yupipi93/arduino-lemon-piano/versions/v5.5-power-filter/firmware/probe/README.md

# Board probe — v0.7.1 PCB

Not a game and not a version: a diagnostic firmware for the **assembled
v0.7.1 board**, for when it boots, lights its LEDs, and plays nothing.

```bash
# The one to use when nobody is standing at the board yet:
nohup ./run-when-ready.sh pcb 60 >/tmp/probe.log 2>&1 &

# The one to use when you ARE at the board, hand on the fruit:
./run.sh pcb              # ...or ./run.sh proto for the breadboard
```

**`run-when-ready.sh` is the default, and the reason is not politeness.** A
measurement that needs a person's hands is not ready when the machine is ready;
it is ready when the person says so. It flashes the board, sends two buttons to
Sergio's phone, and then sits there — for hours if need be — until he taps
"estoy delante". Only then does it record. `run.sh` starts recording the instant
it is launched, which is correct **only** if someone is already playing.

On 2026-09-13 an agent got this backwards: it started a 160 s capture and then
messaged him to go and play. His answer is the rule now — *"no puedes esperar
que esté yo siempre disponible, no soy una máquina, soy un humano que tiene un
hijo y responsabilidades."* The machine waits for the human, never the reverse.

> **2026-09-12, from the bench:** questions 1 and 2 below are **already
> answered** on the real board — every boot sound plays, and both SENS buttons
> beep when pressed. SENS− lives on A7 and only works through R18, a pull-up to
> `/+5V` in the same row as R1–R7, so that one press also proves **the 5 V rail
> reaches the key pull-ups**. Buzzer, buttons, LEDs and rail are all alive.
> Exactly one block is dead: the seven key channels. Question 3 is the whole
> job now, and it is the one this probe was written for.

It answers three questions in one flash, in this order:

1. **Does D13 drive BUZ1?** It beeps for 400 ms at startup, before anything can
   go wrong. D13 is also the Nano's on-board `L` LED — so *L lit, no sound* is a
   transducer fault (wrong buzzer type, or something low-impedance on J5), and
   *neither* is D13 itself or a badly seated Nano.
2. **Does the +5 V rail reach the pull-ups?** The calibration block prints each
   channel's baseline. Near **1022** is healthy. Near 0 means R1–R7 or the rail
   are not there, and it says so.
3. **Do the keys move at all, and in which direction?** All seven channels at
   10 Hz, raw value and signed delta, plus — every 10 s — the largest excursion
   since boot **in both directions** and a one-line verdict. Three outcomes,
   three different faults:

   | Verdict | Means |
   |---|---|
   | biggest movement **DOWN** | this board's polarity. The game can work; only the margin needs tuning. |
   | biggest movement **UP** | the rig is the V4/V4.5 front end (pin floating, resistor in series, player on +5 V). The game firmware cannot see it, and neither can smart adjust. |
   | **nothing moves** (≤ 2 counts) | no touch signal exists to threshold, whatever the margin says. |

   The probe is deliberately direction-agnostic because the game is not. Both
   front ends use 220 Ω — the value is the same on the breadboard and on the
   board — so "same resistors" does not mean "same circuit", and only the sign
   of the movement tells them apart.

**Run it on the breadboard too.** Same sketch, same Nano, same 9600 baud. Two
screenshots settle in a minute what no amount of reading the docs can: if the
working rig's numbers go UP and the board's do not move, the topologies differ
and that is the entire fault.

It also prints the two SENS buttons' state, which should read `up` with nothing
pressed. Permanently `DOWN` means SW1/SW2 are shorted to GND — see §4 of
[../../../../pcb/docs/REVIEW-v0.7.1-silent-keys.md](../../../../pcb/docs/REVIEW-v0.7.1-silent-keys.md).

**Why not `-DDEBUG_TOUCH` on the game build?** Because that prints only on an
*accepted* press, so it prints nothing at all when the fault is that no press is
ever accepted.

Each channel is read twice and the first conversion discarded. At 220 Ω that
changes nothing; it matters the moment the pull-ups are raised, which is the fix
the review proposes.
