yupipi93/arduino-lemon-piano/pcb/docs/DESIGN_STATE.md

# DESIGN_STATE.md — Lemon Piano V5.5 Board

**Current version: v0.7.1 — cosmetic PATCH on v0.7.0: a large
**"Created with ♥ by Multitec." maker's mark fills the top-left free
rectangle on F.SilkS (ADR-038); the board (placements, netlist, holes,
schematic) is byte-for-byte v0.7.0. v0.7.0 itself — the Nano turned back to
mini-USB WEST
(ADR-035), so the digital column is the north row and the analog column the
south row: ten-LED bar on the NORTH edge (centred on x=150, **LED1 at the
east** under D2 — ADR-036), lemon-key header on the SOUTH edge (centred,
**KEY1 west** under A0), the USB-cable corridor (x < 130.4, y 113..127)
reinstated and part-free so the cable leaves the enclosure on the left with
the module seated, and the power-entry filter folded around it — C1 ‖ C3
still adjacent on the north row, D2 + L1 moved down into the south strip with
J1 → D1 (ADR-037). Everything east of the socket (SENS±, J3/J4, BUZ1, J5) is
unchanged from v0.6.0.** (2026-09-06)

> **Flashing note (v0.7.0):** the ADR-030 cost is gone. The mini-USB faces
> west into a part-free corridor, so a cable plugs in with the Nano seated and
> clears the SENS buttons by construction. (v0.5.0–v0.6.0 needed the module
> lifted out of its socket to take a cable.)

> **VU-meter direction (ADR-036, user should know):** with the USB to the
> left, the bar fills **right→left** — LED1 (green) is at the east end, LED10
> (red) at the west. That is what a non-crossing fan under the descending
> D2..D11 row gives; the user's mock-up pasted the v0.6.0 bar (green left)
> without re-deriving it. Reversing it is a ten-line YAML change plus a
> re-route at the cost of a 45-crossing via crossbar.

> **Maker's mark (v0.7.1, ADR-038):** "Created with ♥ by Multitec." sits on
> the top-left silk (two 3.5 mm lines from x=91, spanning the left anchor). The
> heart is a FILLED SILK POLYGON, not a character — KiCad 9's stroke font has
> no U+2665 glyph (it renders as a tofu box), so it is drawn from the classic
> heart parametric. It reached the fab silkscreen gerber as a G36 region fill.

> v0.1.0 ERRATUM (ADR-015): the Nano socket rows were 180°-rotated
> (TX1/VIN assumed at the USB end; the real board has D12/D13 there).
> v0.2.0 corrected the maps. Do not fabricate v0.1.0.

## Block status

| Block | State |
|---|---|
| Nano socket (U1/U2, 2×15) | ✅ CENTRED (pin field x 132.22–167.78), **USB-west**: U1 = analog SOUTH row (pin1 D13 west, rot 90), U2 = digital NORTH row (pin1 TX1 east, rot 270). D12/D13 flank the USB at x=132.22. All 23 used pins netted, 7 NC by design |
| USB-cable corridor | ✅ x < 130.4, y 113..127 part-free on F.Cu (ADR-035 reinstates the ADR-024 band; supersedes ADR-030) — `geometry_gate` checks it against real courtyard boxes |
| Power-entry filter (J1→D1→D2→C1‖C2→L1→C3‖C4) | ✅ WEST block folded around the corridor (ADR-037): **C1 ‖ C3 adjacent** at y=106; **D2 at (107.0, 129.2)** row A; **J1 → D1 at y=136.0** row B; **L1 at (120.0, 134.5)** in its own east column; ceramics on B.Cu at y=112.5 |
| 5 V entry (J1) | ✅ 2-pin 2.54 mm header, SW corner, `+ −` silk above and `5V IN` below (ADR-025) |
| Keyboard (R1–R7 pull-ups + J2 header) | ✅ header CENTRED on the **SOUTH** edge (pin centre exactly x=150), pin 1 = KEY1 at the **WEST** under A0; silk `KEYS 1 2 3 4 5 6 7 G`; pull-ups on B.Cu at y=124.4 just north of the analog row |
| LED bar (D3–D12 + R8–R17) | ✅ **NORTH** strip, CENTRED on x=150, **LED1 EAST → LED10 WEST** (D3 at 170.7 … D12 at 129.3, matching D2..D11 which descend west→east), rot 270 so anodes point south at the row; series R on B.Cu at y=102.97 |
| UI (BUZ1 D13, SW1 SENS+ D12, SW2 SENS− A7 + R18) | ✅ unchanged east block, pair centred on y=120; buzzer NE corner. D13/D12 are at the west end again, so `/BUZZER` ≈ 60 mm and `/SENS_PLUS` ≈ 43 mm (both accepted before: ADR-027/029) |
| Aux speaker out (J5 ∥ BUZ1) | ✅ unchanged (ADR-034). **Piezo or amplified module only** |
| External-button headers (J3 ∥ SW1, J4 ∥ SW2) | ✅ unchanged (ADR-026) |
| Maker's mark (v0.7.1) | ✅ **"Created with ♥ by Multitec."** F.SilkS, top-left free rectangle (x 91..129, y 114..124), 3.5 mm / 0.40 mm stroke, heart = filled `gr_poly` (ADR-038). Left anchor divider split around it. No pad/net/copper change |
| GND | ✅ B.Cu zone, solid connect on all GND pads; refilled after the width pass (no split-net repair was needed this run) |
| Mounting (H1–H4, M2) | ✅ (95,105) / (205,105) / (95,135) / (205,135), symmetric about x=150 and y=120 |
| Schematic | ✅ mirrors PCB (48 symbols incl. 3 PWR_FLAGs), ERC 0/0. Unchanged by the flip — the pin→net map is electrical, only placements moved |
| Fab package | ✅ `pcb/releases/v0.7.1/lemon-piano-v0.7.1-fab.zip` (14 files), generated by `/fab` from the exact board every gate passed on |

## Verification snapshot (v0.7.1)

| Gate | Result |
|---|---|
| Cloud `/drc` | **0 errors, 0 warnings, 0 unconnected** (`validation/drc-v0.7.1.json`; `included_severities` = error + warning, `schematic_parity` empty) |
| ERC | 0 errors, 0 warnings (`validation/erc-v0.7.1.txt`) |
| `verify_placement` (C1 chirality, C2 flip, C3 pad↔net↔function, C4 net intent) | **74 OK / 0 FAIL** — after re-deriving both flipped 0805 groups' pad numbers from the built board (first run failed exactly there, as AGENT_PROMPT predicts) |
| `verify_holes` (geometric + VISION) | PASS — vision ran on both sides, max leave-one-out error 0.022 mm |
| `geometry_gate` (30 checks: outline, hole symmetry, USB-west orientation, LEDs north + centred + LED1 east, keys south + centred + KEY1 west, **corridor part-free**, filter-in-west, C1/C3 adjacency, button-pair centring, EXT headers east, J5-adjacent-to-BUZ1, copper per net, courtyards) | ALL PASS |
| Extra logical pass (independent script over the routed `.kicad_pcb`) | PASS — every Nano pin's net matches NETLIST.md, D12/D13 at x=132.22 (USB end), LED fan and keys fan both monotonic (no crossings), zero F.Cu pads in the corridor, all 34 nets have copper, both pin-legend rows read in true pin order |
| Render inspection (top+bottom, 4 styles) | PASS — overlay photo lands **USB-west** unrotated (PIL_rot 0), every part shows a 3D body (D1 included), LED colours 10→1 = red red orange orange yellow yellow yellow green green green west→east |
| post_route widths | 116 segments at target, 15 short pad-entry stubs capped (all ≥ 0.2 mm, worst case ≈ 200 mA); 1 dangling `/BUZZER` spur removed; no split net; 1 zone refill. 131 segments, 1 via |
| Maker's-mark silk (v0.7.1) | verified on the ROUTED board: both credit lines on F.SilkS (unmirrored, 3.5 mm), heart a 96-pt filled `gr_poly` with its point at the bottom, zero silk over any pad; the F_Silkscreen fab gerber carries the heart as a G36 region fill; render-diff vs v0.7.0 shows the two new text lines in the top-left and nothing else moved |
| Idempotency | `build_board` byte-identical across two scratch runs (`53d8c86a46ea`); routed board `65058595dd8c` |

## Iteration history

| Version | What changed | DRC (err/warn/unconn) | Verdict |
|---|---|---|---|
| v0.0.1 | first placement (no routing) | 0 / 44 / 81 | placement fits; silk collisions; renders verified |
| v0.0.2 | first freerouting pass + naive width post-pass | 12 / 44 / 9 | starved thermals on SMD GND pads; widening broke clearances |
| v0.0.3 | solid zone-connect on all GND pads; clearance-aware widener | 0 / 44 / 0 | electrically clean; silk collisions remain |
| v0.0.4 | silk labels/refs repositioned, SW refs hidden | 0 / 25 / 0 | all remaining warnings = text height < 0.8 |
| v0.0.5 | all silk text ≥ 0.8 mm | 0 / 4 / 0 | title/BUZ1 silk clashes + 1 dangling freerouting spur |
| v0.0.6 | title split, BUZ1 ref inside circle, dangling-spur cleaner | **0 / 0 / 0** | fully clean; all gates pass |
| v0.1.0 | release: schematic+ERC, gates wired into pipeline, island-healing guard, /fab | **0 / 0 / 0** | released, later found ERRATUM ADR-015 — do not fabricate |
| v0.2.0 | REAL Nano orientation (ADR-015): keys header south, LED bar north (E→W); post_route self-healing upgrades (ADR-018) | **0 / 0 / 0** | released + render suite via API v0.3.0 |
| v0.2.1 | 'pcb' version label, per-pin silk legends (both rows), all component refs visible per layer, suite naming normal/dim/realistic/overlay | **0 / 0 / 0** | released |
| v0.3.0 | 4 anchor holes (ADR-020), VU-meter LED colors + 3D bodies (ADR-021), /place model-strip bugfix (ADR-022), brighter Nano photo (ADR-023), hole VISION pass (LL §22) | **0 / 0 / 0** | released |
| v0.4.0 | 120 × 40 mm frame + floor-plan remake (ADR-024): Nano centred, keys centred south, filter folded around a USB corridor, D2 at rot=180; 2-pin 5 V header (ADR-025); parallel EXT headers J3/J4 (ADR-026); buzzer NE (ADR-027); title in the corridor (ADR-028) | **0 / 0 / 0** | released (superseded by v0.5.0) |
| v0.5.0 (run 1) | Nano FLIPPED to USB-east (ADR-029), keys north, LED bar south + centred, USB keepout dropped (ADR-030), filter refactored with C1 ‖ C3 adjacent (ADR-031) | 2 / 0 / 0 | **FAILED the DRC gate** — two `/+5V` bus bridges laid on filled ground |
| v0.5.0 (run 2) | post_route now refills the GND zone after split-net repair (ADR-032) | **0 / 0 / 0** | released |
| v0.5.1 | D1's 3D body restored (ADR-033). Cosmetic only | **0 / 0 / 0** | released |
| v0.6.0 | J5: 2-pin aux speaker output in parallel with the buzzer (ADR-034) | **0 / 0 / 0** | released |
| v0.7.0 (run 1) | Nano turned back to **USB-west** for enclosure cable access (ADR-035, supersedes ADR-029/030): LEDs north with LED1 east, keys south with KEY1 west (ADR-036), USB corridor reinstated, D2 + L1 moved to the south strip (ADR-037) | **0 / 0 / 0** | DRC/ERC/renders/3D green; **stopped at `verify_placement`** — both 0805 groups' pad numbers inverted with the flip (expected, AGENT_PROMPT step 2) |
| v0.7.0 (gates re-run) | `ground-truth/components.yaml` pad numbers re-derived from the built board (no board change); verify_placement 74/0, verify_holes + vision PASS, geometry_gate 30/30; `/fab` on that same board | **0 / 0 / 0** | released |
| v0.7.1 | cosmetic silk PATCH: "Created with ♥ by Multitec." maker's mark, top-left, heart as a filled polygon (ADR-038). No placement/net/hole change — all three gates identical to v0.7.0 | **0 / 0 / 0** | **RELEASED** |

(One v0.1.0 route attempt produced a GND-zone island — caught by the
DRC gate, fixed by the automatic island healing, re-run clean. Kept in
`validation/` history.)

## How to regenerate

```bash
# full iteration (build → /place → /route → post → /drc → /render → gates):
./pcb/tools/cloud_pipeline.sh v0.7.1
# release (adds /fab):
./pcb/tools/cloud_pipeline.sh v0.7.1 --fab
```

Note on v0.7.0's release: the fab package was produced by calling `/fab`
directly on the board that had just passed every gate, rather than by a
`--fab` re-run of the whole pipeline. Freerouting is stochastic, so a
re-run would have routed a *different* board and needed the full gate set
again; fabbing the verified artefact keeps the release byte-consistent with
the committed `.kicad_pcb` (the v0.5.0 lesson in AGENT_PROMPT).

## Open items

- Bench-validate the filter on the physical board (the V5.5 repo's own
  pending check — switch-flipping session with the V5 bench sampler).
- **VU-meter direction** (ADR-036): the bar fills right→left with the USB on
  the left. If the user prefers green-left, reverse D3..D12 / R8..R17 /
  the B.SilkS LED refs in the YAML and re-route (expect ~10 vias and a
  carved B.Cu plane under the north row).
- The mini-USB plug's overmold is ~11 mm wide; the corridor reserves ±7 mm
  about y=120 on F.Cu. Tracks do cross it (that is by design), so a
  right-angle plug is fine but nothing tall may ever be placed there again.
- The 15 capped stubs (ADR-008) are ≥ 0.2 mm and current-safe.
- **J5 drives what D13 drives**, i.e. a high-impedance piezo (ADR-034).
- `/VRAW` and `/+5V` now run ≈ 30 mm north–south side by side through the
  west block (ADR-037). Acceptable for a conducted-transient filter; the
  C1—L1—C3 series order of ADR-031's note remains the fix if HF isolation
  is ever needed.
- Largest free areas: the region under the Nano body on both layers and the
  east half of the south strip (x 128–139, y 129–140) beside L1.
