yupipi93/arduino-lemon-piano/pcb/docs/NETLIST.md

# NETLIST.md — Lemon Piano V5.5 Board

Ground truth for the PCB. Extracted 2026-07-30 from the `arduino-lemon-piano`
repo — **no value, pin or part invented here**. Sources:

| Source | What it fixes |
|---|---|
| `versions/v5.5-power-filter/HARDWARE.md` | power-entry filter chain, part values, BOM delta |
| `versions/v5-led-bar/HARDWARE.md` (pin map, 2026-07-28) | every Nano pin assignment |
| `tools/wiring_diagrams.py` → `build_v5_5()` (DRC-validated wirewright contract) | the authoritative net list (58 nets rendering, 0 violations) |

> The V5 HARDWARE.md *BOM table* contains two stale rows ("Passive buzzer D8",
> "SENS + on D7"). The 2026-07-28 pin map in the same file and the
> `build_v5_5()` contract agree and override them: **buzzer = D13,
> SENS + = D12, SENS − = A7**. Recorded in DECISIONS.md (ADR-001).

## Circuit summary

V5 game board (7 lemon keys pulled up 220 Ω to the rail, player holds GND;
ten-LED progress bar on D2–D11; SENS± buttons; passive buzzer) **plus** the
V5.5 power-entry filter: 5 V in → P6KE6.8A TVS shunt → 1N5817 series Schottky
→ 470 µF ‖ 100 nF → 100 µH power choke → 470 µF ‖ 100 nF → the +5 V rail
(also AVcc = ADC reference — that is the whole point of the filter).

The Nano is **socketed**: two 1×15 2.54 mm female rows (U1/U2). Since v0.7.0
the mini-USB end faces the **WEST** board edge again (ADR-035, undoing the
v0.5.0 flip): the cable leaves the enclosure on the left, clear of the button
block, and a part-free corridor (x < 130.4, y 113..127) lets it be plugged in
with the module seated. USB power still stays behind the 1N5817 so it cannot
back-feed the filter (`HARDWARE.md` powering rule 2).

**v0.4.0 circuit deltas** (user spec 2026-07-30, ADR-024…027) — the V5.5
circuit itself is unchanged; only the board interface grew:

- 5 V entry is a **2-pin 2.54 mm header** (J1) instead of the Phoenix screw
  terminal. Same two nodes, same polarity (pad 1 = +, pad 2 = GND).
- Two **external-button headers** (J3, J4) are wired in **parallel** with
  SW1/SW2. Shorting a header's two pins is electrically identical to
  pressing the on-board button, so a panel-mounted button can be added
  without cutting a trace.
- **v0.6.0**: an **auxiliary speaker header** (J5) is wired in **parallel**
  with the buzzer — pad 1 on /BUZZER, pad 2 on /GND. It carries the raw D13
  drive, so it suits another passive piezo or an *amplified* speaker module;
  a bare 4–8 Ω voice coil must not be connected directly (ADR-034).

## Components (29 + 18 R + 4 H = 51 footprints)

| Ref | Value | Footprint (KiCad 9 lib) | Source line |
|---|---|---|---|
| U1 | Nano socket row A — the **analog** column (Nano pins 16–30: D13,3V3,AREF,A0…A7,5V,RST,GND,VIN) | `Connector_PinSocket_2.54mm:PinSocket_1x15_P2.54mm_Vertical` | v5 HARDWARE pin map |
| U2 | Nano socket row B — the **digital** column (Nano pins 1–15: TX1,RX0,RST,GND,D2…D12) | idem | idem |
| J1 | 5V_IN 1×2 header | `Connector_PinHeader_2.54mm:PinHeader_1x02_P2.54mm_Vertical` | v5.5 BOM "5 V input pigtail" → 2-pin header (ADR-025, supersedes ADR-003) |
| J2 | LEMON_KEYS 1×8 header (KEY1…KEY7 + GND) | `Connector_PinHeader_2.54mm:PinHeader_1x08_P2.54mm_Vertical` | keys A0–A6 + GND clip (ADR-004) |
| J3 | SENS+_EXT 1×2 header (parallel to SW1) | `Connector_PinHeader_2.54mm:PinHeader_1x02_P2.54mm_Vertical` | user spec 2026-07-30 (ADR-026) |
| J4 | SENS−_EXT 1×2 header (parallel to SW2) | idem | idem |
| J5 | SPK_OUT 1×2 header (parallel to BUZ1) | idem | user spec 2026-07-31 (ADR-034) |
| D1 | P6KE6.8A (TVS, 600 W) | `Diode_THT:D_DO-15_P5.08mm_Vertical_KathodeUp` | v5.5 HARDWARE filter table |
| D2 | 1N5817 (Schottky) | `Diode_THT:D_DO-41_SOD81_P5.08mm_Vertical_AnodeUp` | idem |
| C1 | 470u/16V (input reservoir) | `Capacitor_THT:CP_Radial_D8.0mm_P3.50mm` | idem |
| C2 | 100nF X7R (input ceramic) | `Capacitor_SMD:C_0805_2012Metric_Pad1.18x1.45mm_HandSolder` | idem + CONVENTIONS §4 |
| L1 | 100uH ≥1 A power choke (e.g. Fastron 07HCP-101K, 1.3 A) | `Inductor_THT:L_Radial_D8.7mm_P5.00mm_Fastron_07HCP` | idem ("drum or toroid, ≥1 A") |
| C3 | 470u/16V (output reservoir) | `Capacitor_THT:CP_Radial_D8.0mm_P3.50mm` | idem |
| C4 | 100nF X7R (output ceramic) | 0805 HandSolder | idem |
| R1–R7 | 220 (key pull-ups KEY1…KEY7 = A0…A6) | `Resistor_SMD:R_0805_2012Metric_Pad1.20x1.40mm_HandSolder` | v5 HARDWARE "220 Ω pull-up per key" |
| R8–R17 | 220 (LED series, LED1…LED10) | idem | v5 HARDWARE "one per LED" |
| R18 | 10k (SENS− external pull-up on A7) | idem | v5 HARDWARE "A7 has no internal pull-up" |
| D3–D12 | LED 1…10: 3×GREEN, 3×YELLOW, 2×ORANGE, 2×RED | `LED_THT:LED_D3.0mm` (colored 3D bodies per LED, ADR-021) | v5 HARDWARE "Green LEDs ×10"; VU-meter colors per user spec 2026-07-30 |
| BUZ1 | passive buzzer | `Buzzer_Beeper:Buzzer_12x9.5RM7.6` | v5 HARDWARE (D13) + CONVENTIONS §5 |
| SW1 | SENS + push button (D12, to GND, internal pull-up) | `Button_Switch_THT:SW_PUSH_6mm` | v5 HARDWARE pin map |
| SW2 | SENS − push button (A7, to GND, R18 pull-up) | idem | idem |
| H1–H4 | M2 mounting hole | `MountingHole:MountingHole_2.5mm_Pad_Via` | board spec v0.3.0 (2 per short edge, ADR-020) |

## Board frame (v0.7.0)

120 × 40 mm, KiCad frame x 90..210 / y 100..140, centre (150, 120). The
Nano pin field is centred on the board (x 132.22..167.78, rows y 112.38 /
127.62) with the **mini-USB facing WEST** (ADR-035); that puts the digital
column on the north row and the analog column on the south row.
Consequently the LED bar sits on the NORTH edge (centred on x = 150, LED1 at
the east under D2) and the keys header on the SOUTH edge (centred, pin centre
exactly x = 150, KEY1 at the west under A0). The power-entry filter occupies
the west block folded around the USB-cable corridor (x < 130.4, y 113..127,
part-free on F.Cu): C1 ‖ C3 on the north row, D2 / J1 → D1 / L1 in the south
strip (ADR-037).

## Nano socket pin map (physical, USB end = WEST) — v0.7.0, ADR-035

The Nano's own pinout is fixed (ADR-015: D12/D13 flank the mini-USB,
TX1/VIN sit at the ICSP end). v0.7.0 turns the module 180° in-plane back to
USB-west (v0.5.0/v0.6.0 were USB-east), which swaps BOTH which row carries
which column AND the west→east pin order:

```
U2 (NORTH row, y=112.38), pin1 → pin15 runs EAST → WEST:
   TX1 RX0 RST GND D2 D3 D4 D5 D6 D7 D8 D9 D10 D11 D12
   x:  167.78 …………………………………………………………………… 132.22
        [ mini-USB faces x=90 west edge ]
U1 (SOUTH row, y=127.62), pin1 → pin15 runs WEST → EAST:
   D13 3V3 AREF A0 A1 A2 A3 A4 A5 A6 A7 5V RST GND VIN
   x:  132.22 …………………………………………………………………… 167.78
```

Digitals land on the NORTH row **descending** west→east (D2 at 157.62 …
D11 at 134.76) → LED bar on the NORTH edge with **LED1 at the EAST** under
D2 and LED10 at the west under D11, so the fan does not cross (ADR-036).
Analogs land on the SOUTH row **ascending** west→east (A0 at 139.84 … A6 at
155.08) → keys header on the SOUTH edge with **J2 pin 1 (KEY1) at the WEST**
under A0 (x 141.11 vs 139.84). D13 and D12 sit at the WEST end flanking the
USB, so `/BUZZER` (D13 → BUZ1 in the NE corner) is long again, as in v0.4.0
and accepted in ADR-027, and so is `/SENS_PLUS` (D12 → SW1).

## Historical pin map (USB end = EAST) — v0.5.0 … v0.6.0, ADR-029

Flipping the module 180° in-plane swapped BOTH which row carried which
column AND the west→east pin order:

```
U1 (NORTH row, y=107.38+5 → 112.38), pin1 → pin15 runs EAST → WEST:
   D13 3V3 AREF A0 A1 A2 A3 A4 A5 A6 A7 5V RST GND VIN
   x:  167.78 …………………………………………………………………… 132.22
        [ mini-USB faces x=210 east edge ]
U2 (SOUTH row, y=127.62), pin1 → pin15 runs WEST → EAST:
   TX1 RX0 RST GND D2 D3 D4 D5 D6 D7 D8 D9 D10 D11 D12
   x:  132.22 …………………………………………………………………… 167.78
```

Analogs land on the NORTH row → keys header on the NORTH edge, with
J2 pin 1 (KEY1) at the EAST under A0 (x 158.89 vs 160.16) so the fan does
not cross. Digitals land on the SOUTH row ascending west→east → LED bar on
the SOUTH edge ascending west→east (LED1 west under D2, LED10 east under
D11). D13 and D12 now sit at the EAST end, next to the buzzer and the
SENS+ button respectively — much shorter runs than v0.4.0.

## Historical pin map (USB end = WEST) — v0.2.0 … v0.4.0, ADR-015

**Erratum fixed in v0.2.0**: v0.1.0 assumed TX1/VIN at the USB end (a
misread pinout diagram). The REAL Nano — verified on the official 2008
Arduino Nano V2.2 photo (Wikimedia `File:ArduinoNanoTop.jpg`) and on
clone boards (`File:Arduino Nano.jpg`) — has **D12/D13 flanking the
mini-USB and TX1/VIN at the ICSP end**. With the USB facing WEST:

```
   x=104                                                    x=139.56
U2: D12 D11 D10 D9 D8 D7 D6 D5 D4 D3 D2 GND RST RX0 TX1   (y=107.38, pin15→pin1)
        [ mini-USB faces x=90 west edge ]
U1: D13 3V3 AREF A0 A1 A2 A3 A4 A5 A6 A7 5V RST GND VIN   (y=122.62, pin1→pin15)
```

`U1` = SOUTH row, pin 1 (D13) west; `U2` = NORTH row, pin 1 (TX1) east.
Analogs land on the SOUTH row → keys header on the SOUTH edge; digitals
on the NORTH row → LED bar on the NORTH edge (both flipped vs v0.1.0).

## Nets (KiCad net number → name → pads)

| # | Net | Pads |
|---|---|---|
| 1 | /+5V | U1.12 (5V), L1.2, C3.1(+), C4.1, R1.2…R7.2, R18.2 |
| 2 | /GND | U1.14, U2.4, J1.2, J2.8, J3.2, J4.2, J5.2, D1.2(A), C1.2(−), C2.2, C3.2(−), C4.2, R8.1…R17.1, BUZ1.2, SW1.2(×2), SW2.2(×2), H1.1…H4.1 |
| 3 | /VIN | J1.1(+), D1.1(K), D2.2(A) |
| 4 | /VRAW | D2.1(K), C1.1(+), C2.1, L1.1 |
| 5–11 | /KEY1…/KEY7 | U1.4…U1.10 (A0…A6), R1.1…R7.1, J2.1…J2.7 (KEY1=J2.1 … KEY7=J2.7) |
| 12 | /SENS_MINUS | U1.11 (A7), R18.1, SW2.1(×2), J4.1 |
| 13 | /SENS_PLUS | U2.15 (D12), SW1.1(×2), J3.1 |
| 14 | /BUZZER | U1.1 (D13), BUZ1.1(+), J5.1 |
| 15–24 | /LED1…/LED10 | U2.5…U2.14 (D2…D11) → D3.2…D12.2 (anodes) |
| 25–34 | /LED1_K…/LED10_K | D3.1…D12.1 (cathodes) → R8.2…R17.2 |

Unconnected (by design): U2.1 (TX1), U2.2 (RX0), U2.3 (RST), U1.2 (3V3),
U1.3 (AREF), U1.13 (RST), U1.15 (Nano VIN — the filtered rail feeds the 5V
pin directly, exactly like the breadboard rail; VIN would insert the Nano's
own regulator and drop the 4.7 V rail further).

Wirewright-contract cross-check (`build_v5_5`): net `vin` = {J1.vout,
DTVS.cathode, DS.anode} ✓ /VIN; `vraw` = {DS.cathode, CF1.a, CF2.a, LF1.a} ✓
/VRAW; `vfilt` = {LF1.b, CF3.a, CF4.a, rail 5V} ✓ /+5V; `pgnd` + `nanognd` +
key/button/LED grounds ✓ /GND; `kn0..kn6` (pin+fruit clip+pull-up low side)
✓ /KEY1…7; `a0..a9`/`c0..c9`/`g0..g9` ✓ /LEDn + /LEDn_K; `buzsig` ✓ /BUZZER;
`SUPsig` ✓ /SENS_PLUS; `sdnsig` (A7+button+R.b) ✓ /SENS_MINUS; `sdnpu`/`kp*`
(pull-up highs) ✓ /+5V. All 58 diagram nets accounted for.

## Current / width budget

Worst case board draw ≈ 200 mA (10 LEDs ≈ 150 mA + Nano ≈ 30 mA + margin —
v5 HARDWARE "All ten lit ≈ 150 mA"). Power path (VIN→VRAW→+5V, GND returns)
routed at 0.5 mm (≥ 0.4 spec); signals 0.25 mm. LED/key currents ≤ 15 mA.
