yupipi93/arduino-lemon-piano/docs/GUIA-DE-USO.es.md

# 🍋 Piano de limones — cómo se toca

*La hoja de instrucciones, pensada para imprimirse y dejarse al lado del piano.
Explica la caja que tienes delante y no da por supuesto nada del código de
dentro.*

> Este repositorio se escribe en inglés; el original de esta hoja es
> [USER-GUIDE.md](USER-GUIDE.md) y es la fuente. Esta traducción existe porque
> lo que se imprime lo lee gente, y la gente que lo va a leer habla español.
> Si las dos discrepan, manda la inglesa.

Vale para la placa **V5.5** (la que va en la carcasa impresa) con el firmware
del 09-09-2026.

---

## 1. Montarlo

1. Clava un clavo en cada uno de los siete limones y engancha un cable a cada
   clavo, de izquierda a derecha: son las teclas **1** a **7**.
2. El octavo cable — el que sobra — va a la **pinza**, y **la pinza se sujeta
   con la mano**. No es opcional: tú eres la mitad del circuito. Hasta que
   alguien no la tiene en la mano, no funciona nada.
3. Aliméntalo con un **cargador de pared USB**, no con un portátil. El ruido de
   masa de un ordenador se salta el filtro y el piano empieza a tocar solo.
4. Toca un limón con la otra mano. Suena.

> **Si no pasa nada, o si toca sin que lo toquen**, vete al §6 *Ajuste*. La
> fruta cambia según se seca; el piano está hecho para reajustarse.

## 2. Al encenderlo

La barra de diez luces se llena sola durante un par de segundos y suena una
moneda por cada limón. Eso es la **calibración**: está midiendo qué aspecto
tiene "no me están tocando" en cada limón.

**No toques la fruta mientras corren las luces.** Si tienes un limón cogido
durante esos dos segundos, aprende eso como lo normal y esa tecla se queda
sorda.

Una fanfarria corta y después una melodía: así te dice **en qué modo ha
arrancado**. Siempre arranca en el **nivel 1**.

## 3. El juego

Cada nivel esconde una **melodía secreta de diez notas**. Hay que encontrarla de
oído.

- Toca limones libremente: no pasa nada malo y la barra sigue vacía.
- En cuanto aciertes la **primera nota de la melodía secreta**, se enciende la
  luz 1. Ya estás dentro.
- Cada nota correcta enciende la siguiente. **1 → 10.**
- Una nota equivocada **apaga la barra entera** y hay que empezar la melodía de
  nuevo. Primero oyes la nota que has tocado y después el sonido de error, así
  que siempre sabes qué limón ha sido.
- Enciende las diez y suena el tema del nivel, con las luces subiendo, después
  la fanfarria del mástil — y **el siguiente nivel empieza solo**.
- Al superar el nivel 4 la melodía final se repite en bucle hasta que la pares
  (ver §5).

**Tocar el mismo limón dos veces seguidas no es un fallo: simplemente no
cuenta.** La nota suena igual de bien; el juego no la está escuchando, porque ya
está esperando un limón *distinto*.

Y se ve que no ha contado: **se encienden todas las luces a la vez** mientras
tienes ese limón tocado, y en cuanto lo sueltas tu marcador vuelve exactamente
como estaba. Diez luces encendidas nunca son un marcador: diez es ganar, y al
ganar no te quedas con el dedo puesto. No pierdes nada, no se te resta nada, y
ya no hay sonido de regañina: ese traqueteo se ha quitado (13-09-2026).
Compáralo con una nota equivocada, que **apaga la barra y la deja apagada**: no
se pueden confundir.

## 4. Modo libre — el piano sin juego

El modo libre no es un nivel y **no se llega a él jugando**. **Mantén pulsado el
botón + tres segundos** y el piano cambia el juego por el instrumento. Vuelve a
mantenerlo y el juego regresa, al nivel que dejaste.

En modo libre los siete limones son sencillamente las notas de toda la vida:

| Limón | 1 | 2 | 3 | 4 | 5 | 6 | 7 |
|---|---|---|---|---|---|---|---|
| Nota | **do** | **re** | **mi** | **fa** | **sol** | **la** | **si** |
| | C5 | D5 | E5 | F5 | G5 | A5 | B5 |

- Ni melodía secreta, ni notas equivocadas, ni nada que ganar.
- **Puedes repetir el mismo limón las veces que quieras**: aquí la regla de "una
  sola vez" está desactivada, porque es justo lo contrario de lo que necesita un
  instrumento.
- **Si mantienes el limón, la nota se mantiene: una nota, no un tartamudeo.**
  Suelta de verdad y vuelve a tocar para que suene otra vez. Tocar rápido sigue
  funcionando; sólo ignora el parpadeo de un dedo que nunca se fue.
- **Cada nota rompe una ola.** Al tocar un limón sale una ola de luz desde el
  sitio que ese limón ocupa en la barra: el limón 1 la manda de izquierda a
  derecha, el 7 de derecha a izquierda, y uno del medio la abre hacia los dos
  lados a la vez.
- Y eso es **todo** lo que hacen las luces aquí: pasa la ola y la barra se
  vuelve a apagar. No se queda nada encendido mientras mantienes la nota.
- **Dos limones a la vez suenan como dos notas.** Mantén un segundo limón junto
  al primero y suena el intervalo, con la barra enseñando dos luces separadas,
  una por nota. Suelta cualquiera de los dos y el otro sigue sonando. Hacen
  falta dos toques de verdad: un dedo apoyado cerca del limón vecino no vale, y
  eso es a propósito.
- Cuando no estás tocando, la barra está **apagada**. Toda luz que veas la ha
  encendido tu dedo.
- Entrar en modo libre lo anuncia la propia barra: dos luces entran desde los
  extremos, se encuentran, se abren hasta encender la barra entera y se apagan
  — y después el piano te toca la escala.

### ¿Se te ha olvidado cómo iba la melodía? Pídela otra vez

**Toca el mismo limón cinco veces seguidas** y el nivel te vuelve a tocar su
melodía, la misma con la que empezó. En esa melodía está escondida la clave
secreta, así que esto es el botón de pista.

**La nota que acabas de tocar cuenta como la primera**, así que en la práctica
son cuatro toques más sobre el limón que ya tienes debajo del dedo. Toca,
suelta, vuelve a tocar; sin pararte, porque si dejas más de segundo y medio
entre dos toques la cuenta empieza de cero.

No molesta al juego: las luces vuelven exactamente como estaban y sigues por
donde ibas. Y hay una forma de que te salga gratis: **repite el limón que el
juego acaba de aceptar.** Tocar dos veces el mismo limón nunca cuenta para
nada, así que hecho de esa manera la pista no te cuesta absolutamente nada.

En modo libre no está, a propósito: tocar un limón una y otra vez es
precisamente para lo que existe el modo libre.

## 5. Elegir modo

Todo lo de aquí abajo se hace con los dos botones: **+** y **−**. La regla que
los hace fáciles de recordar: **un toque es la sensibilidad, una pulsación larga
es un modo.**

### El interruptor del instrumento — mantener **+**

**Mantén pulsado el botón + tres segundos.** Desde el primer segundo la barra se
llena y suena un pitido que sube, igual que en la rueda de abajo, así que
siempre sabes que está cargando. A los tres segundos el piano cambia:

- si estabas jugando un nivel → **modo libre**, anunciado con una escala
  do-re-mi-fa-sol-la-si
- si estabas en modo libre → **vuelta al nivel que dejaste**, anunciado con su
  propio tema

Si lo sueltas antes, no pasa nada. Es un interruptor, así que el mismo gesto te
lleva en los dos sentidos: nunca tienes que buscar un menú para recuperar tu
instrumento.

### La rueda de niveles — mantener **−**

**Mantén pulsado el botón − y no lo sueltes.** Al segundo, el piano empieza a
cargar: la barra se llena y suena un pitido que va subiendo. A los **tres
segundos** las luces hacen un barrido de ida y vuelta, suena un aviso de tres
notas ascendentes y ya estás dentro.

Si lo sueltas antes de los tres segundos no pasa nada: oirás un golpe doble
grave que significa "cancelado". *(La pulsación en sí baja la sensibilidad un
paso, como haría cualquier −; en cuanto se convierte en cambio de modo, ese paso
se devuelve.)*

### Girarla

**Un toque en +** para el nivel siguiente, **un toque en −** para el anterior. Es
una rueda: pasado el nivel 4 se vuelve al 1. El modo libre **no está en la
rueda** — es la pulsación larga de **+**, así que girar la rueda nunca te puede
quitar el instrumento.

Cada parada te dice dónde estás, por partida doble:

| Modo | Luces | Sonido |
|---|---|---|
| Nivel 1 | **1** luz, parpadeando | el tema Overworld |
| Nivel 2 | **2** luces, parpadeando | el tema Underworld |
| Nivel 3 | **3** luces, parpadeando | el tema de la estrella |
| Nivel 4 | **4** luces, parpadeando | el tema del castillo |

Las luces que parpadean son *una pregunta*; las fijas son *un marcador*. "Cuatro luces
parpadeando".

Si vuelves a pulsar mientras suena una melodía, se corta al momento y pasa a la
siguiente: nunca hay que esperar a la música.

### Elegirla

**Pulsa los dos botones a la vez.** Ni el orden ni la precisión importan: pulsa
uno y después el otro cuando quieras. Suena una confirmación corta y arranca el
modo.

Elegir un **nivel** lo empieza desde cero, con la barra vacía. Elegir **modo
libre** te entrega el instrumento.

### Salir sin elegir

Tres maneras, y ninguna cambia nada:

- **Mantén cualquiera de los dos botones tres segundos**: suena el aviso de
  entrada al revés.
- **Márchate.** A los veinte segundos sin tocar un botón se cierra sola.
- **Elige el modo en el que ya estabas**: la rueda se abre justo en el modo que
  estás jugando, así que abrir y aceptar sin más no hace absolutamente nada.

El juego se queda exactamente como lo dejaste: mismo nivel, mismas luces, mismo
progreso.

## 6. Ajuste — cuando la fruta deja de portarse bien

El piano detecta un contacto como una **caída de tres o cuatro cuentas** sobre
1024. Es una señal minúscula, y cambia con la fruta, con la habitación y con tus
manos.

| Síntoma | Qué hacer |
|---|---|
| Los limones no responden | Da unos toques a **+** (más sensible) |
| Toca notas él solo | Da unos toques a **−** (menos sensible) |
| Ni una cosa ni la otra | **Ajuste inteligente**, aquí abajo |
| No funciona absolutamente nada | ¿Tienes la pinza en la mano? ¿Está enchufado a un cargador de pared? |

Cada toque mueve un paso y la barra te enseña dónde queda el ajuste; el tono del
pitido sube según se vuelve más sensible, así que se puede ajustar sin mirar.
Deja el botón pulsado para recorrer los pasos deprisa.

**Ajuste inteligente** — el bueno. **Toca un limón y no lo sueltes**, y entonces
mantén **los dos botones un segundo**. La barra se llena mientras escucha, y
deduce el mejor ajuste con tu dedo de verdad sobre tu fruta de verdad.

- Un acorde ascendente (**1-up**) = ha aprendido algo. Ya está.
- Un traqueteo descendente = no ha podido distinguir tu contacto del ruido, y
  **no ha cambiado nada**. Comprueba que tienes la pinza en la mano y repite.

> **Las tres pulsaciones largas, y cómo no confundirlas.** *Los dos* botones un
> segundo = ajustar. *Sólo* **+** tres segundos = el interruptor del instrumento.
> *Sólo* **−** tres segundos = la rueda de niveles. No pueden chocar: si vas a
> por el segundo botón a media carga, la carga se cancela y le cede el turno al
> ajuste.

Para empezar del todo de cero, **desenchufa y vuelve a enchufar**. Eso repite la
calibración y vuelve al nivel 1.

## 7. Todos los gestos, uno por línea

| Gesto | Qué hace |
|---|---|
| Toque en **+** | Más sensible, un paso — **una luz más** |
| Toque en **−** | Menos sensible, un paso — **una luz menos** |
| Mantener **+** **3 s** | **Modo libre ⇄ el nivel** |
| Mantener **−** **3 s** | **Abre la rueda de niveles** |
| En la rueda: toque en **+** / **−** | Nivel siguiente / anterior (da la vuelta) |
| En la rueda: **los dos botones** | Elegir este nivel |
| En la rueda: mantener cualquiera **3 s** | Salir sin cambiar nada |
| Mantener **los dos** **1 s** tocando un limón | Ajuste inteligente |
| Mantener **los dos** **1 s** durante la melodía final | Volver al nivel 1 |
| Desenchufar y enchufar | Reinicio completo, recalibra |

## 8. Los sonidos y lo que significan

Todo sonido que no es una nota es un efecto de Super Mario Bros, y está
afinado **por encima** de los limones para que nunca se confunda con una nota.

| Sonido | Significado |
|---|---|
| Moneda, una por limón | Calibrando: manos fuera |
| Champiñón (power-up) | Calibración terminada, adelante |
| Pitidos que suben | Un botón está cargando: **+** el interruptor del instrumento, **−** la rueda de niveles |
| Tres notas ascendentes | La rueda está abierta |
| Las mismas tres, descendentes | La rueda se cerró sin cambiar nada |
| Quinta que resuelve en la octava | Has elegido un modo |
| Golpe doble grave | Fin del recorrido, o carga cancelada |
| Estertor corto de muerte | Nota equivocada |
| 1-up | El ajuste inteligente ha aprendido algo |
| Melodía de muerte completa | El ajuste inteligente no ha podido; no ha cambiado nada |
| Fanfarria del mástil | Nivel superado |

---

*Códigos secretos, tablas de notas y el porqué de cada tiempo de arriba:
[../versions/v5.5-power-filter/README.md](../versions/v5.5-power-filter/README.md).*
