yupipi93/arduino-lemon-piano/pcb/renders/INDEX.md

# Renders gallery — renders

> Auto-generated by `pcb-designer gallery renders`. Edit the YAML config or re-run the renderer to update — do NOT hand-edit this file.

Versions catalogued: **36**

## v0.7.1 — realistic

| top | bottom |
|---|---|
| v0.7.1 top | v0.7.1 bottom |

## v0.7.1 — overlay

| top | bottom |
|---|---|
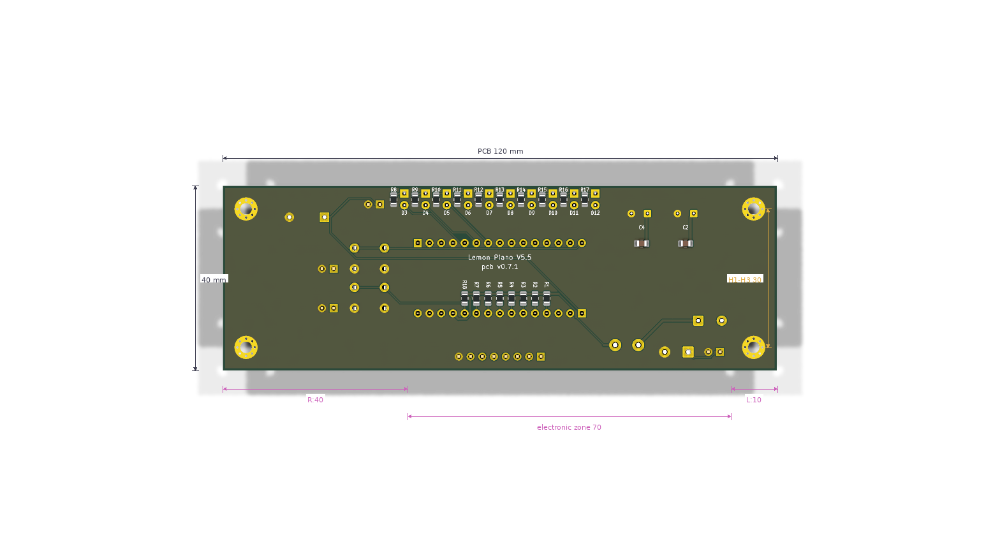
[picture p25: pcb/renders/v0.7.1-overlay-bottom.png]
v0.7.1 bottom
| v0.7.1 top |  |

## v0.7.1 — normal

| top | bottom |
|---|---|
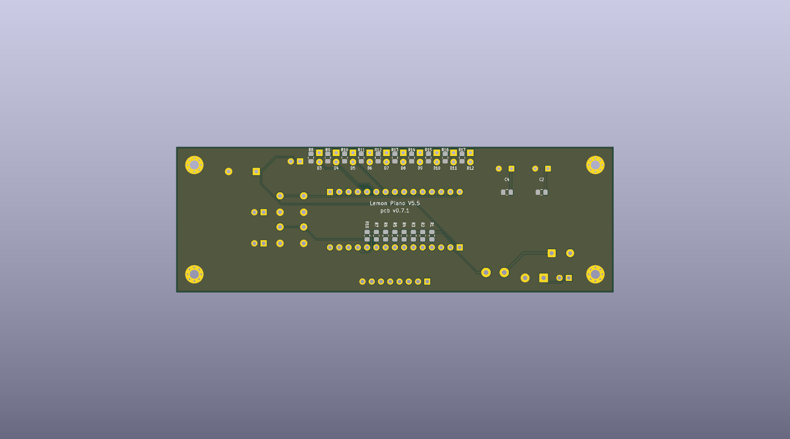
[picture p26: pcb/renders/v0.7.1-normal-bottom.png]
v0.7.1 bottom
| v0.7.1 top |  |

## v0.7.1 — dim

| top | bottom |
|---|---|
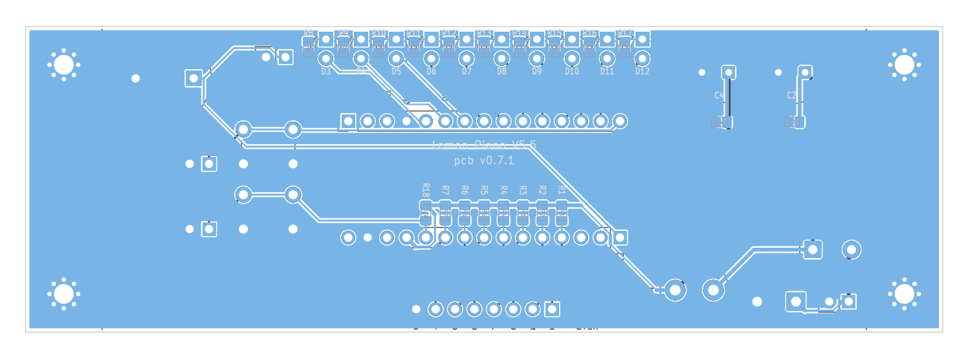
[picture p27: pcb/renders/v0.7.1-dim-bottom.png]
v0.7.1 bottom
| v0.7.1 top |  |

## v0.7.0 — realistic

| top | bottom |
|---|---|
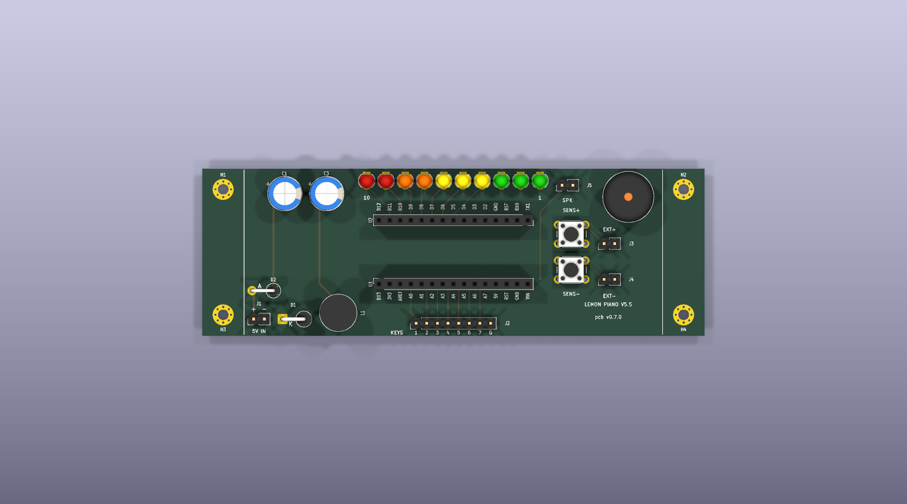
[picture p28: pcb/renders/v0.7.0-realistic-top.png]
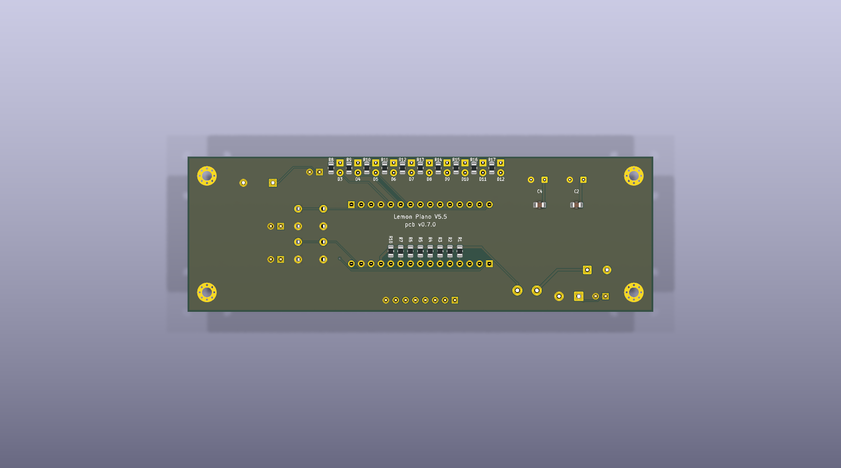
[picture p29: pcb/renders/v0.7.0-realistic-bottom.png]
v0.7.0 bottom
|  |  |

## v0.7.0 — overlay

| top | bottom |
|---|---|
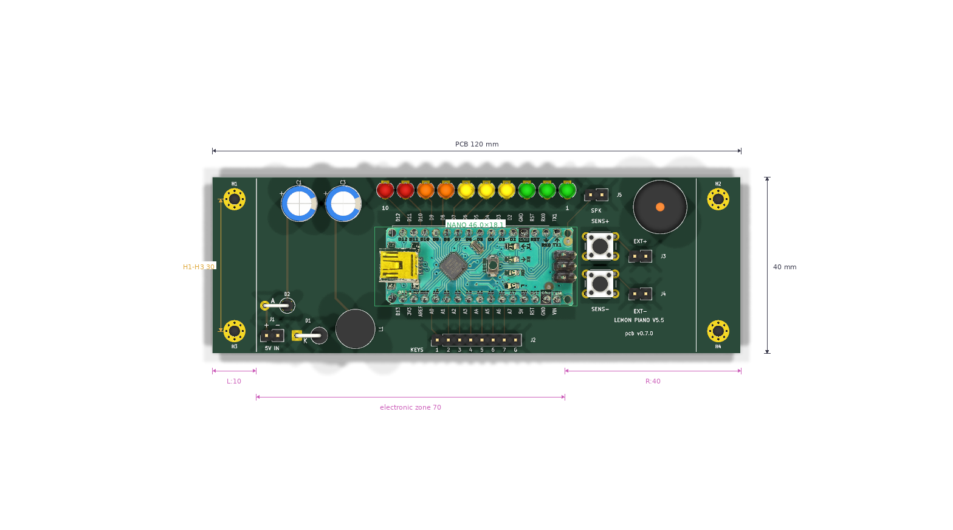
[picture p30: pcb/renders/v0.7.0-overlay-top.png]
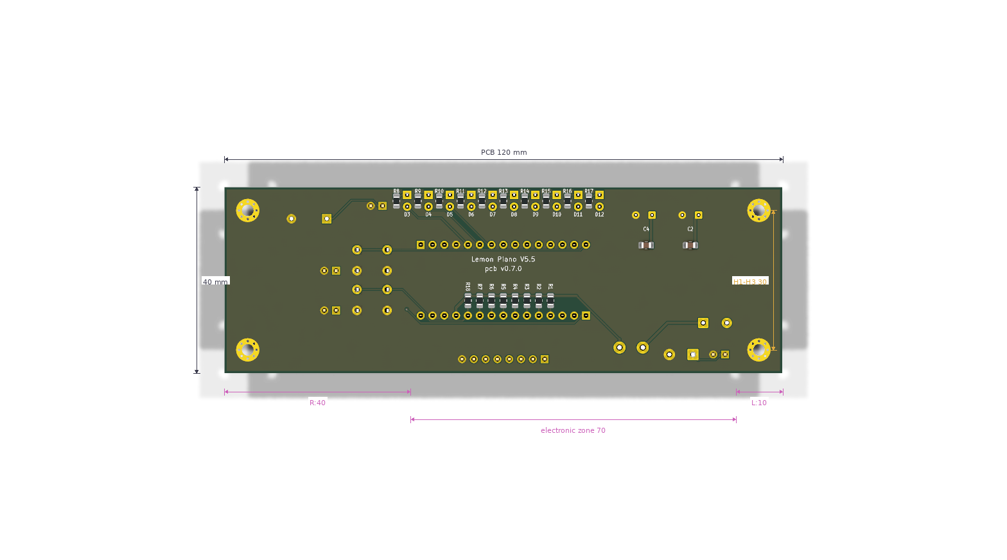
[picture p31: pcb/renders/v0.7.0-overlay-bottom.png]
v0.7.0 bottom
|  |  |

## v0.7.0 — normal

| top | bottom |
|---|---|
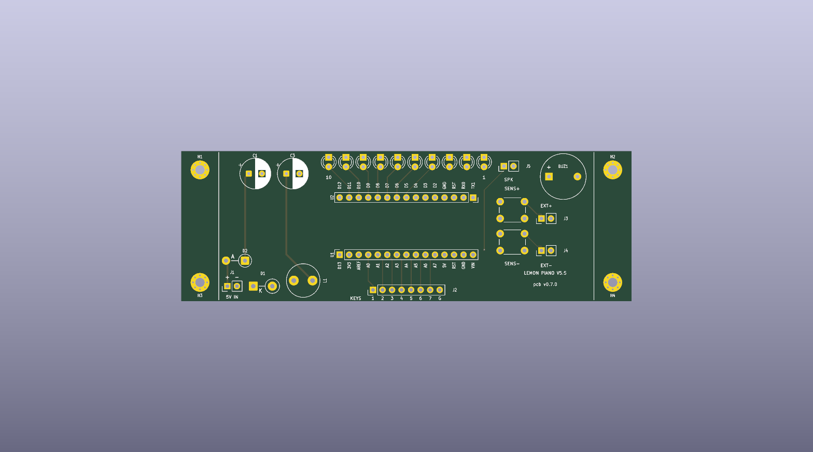
[picture p32: pcb/renders/v0.7.0-normal-top.png]
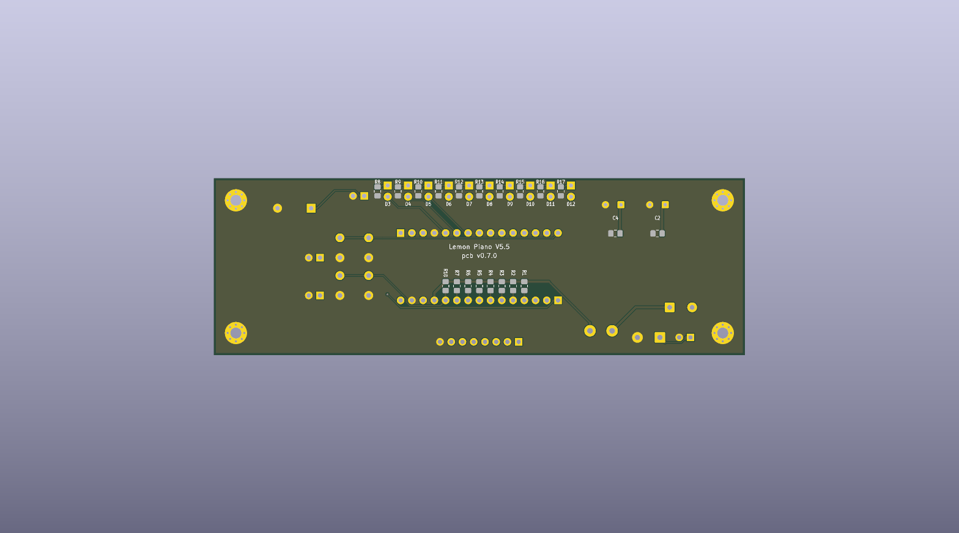
[picture p33: pcb/renders/v0.7.0-normal-bottom.png]
v0.7.0 bottom
|  |  |

## v0.7.0 — dim

| top | bottom |
|---|---|
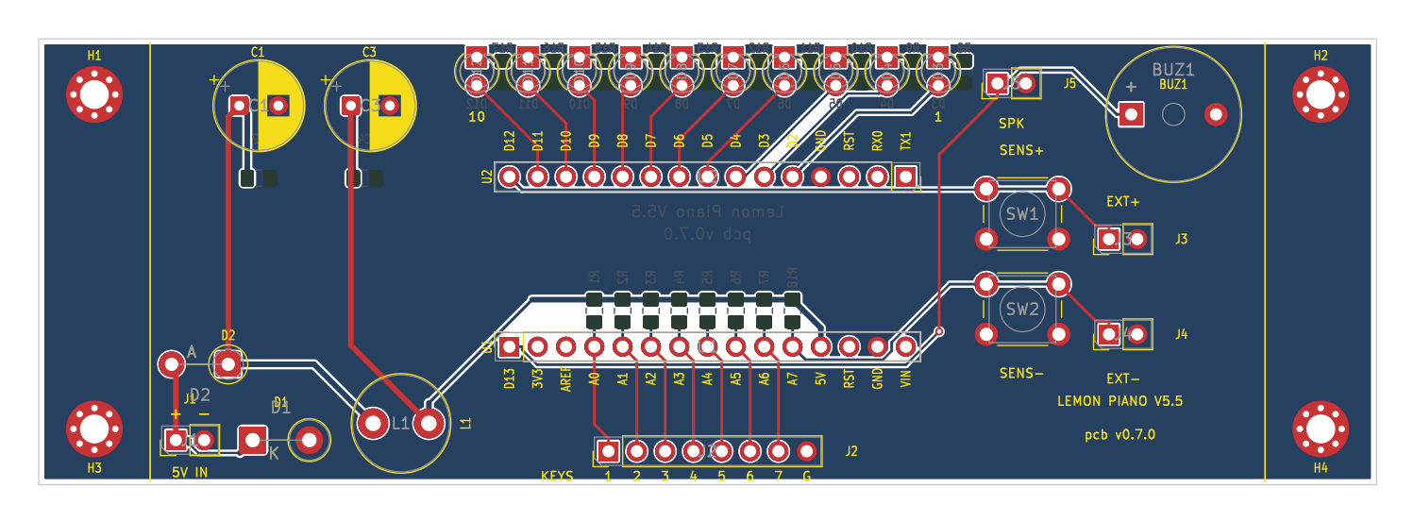
[picture p34: pcb/renders/v0.7.0-dim-top.png]
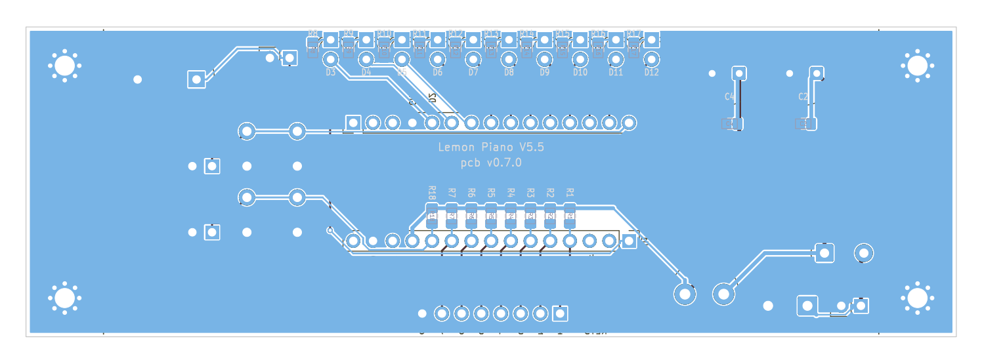
[picture p35: pcb/renders/v0.7.0-dim-bottom.png]
v0.7.0 bottom
|  |  |

## v0.6.0 — realistic

| top | bottom |
|---|---|
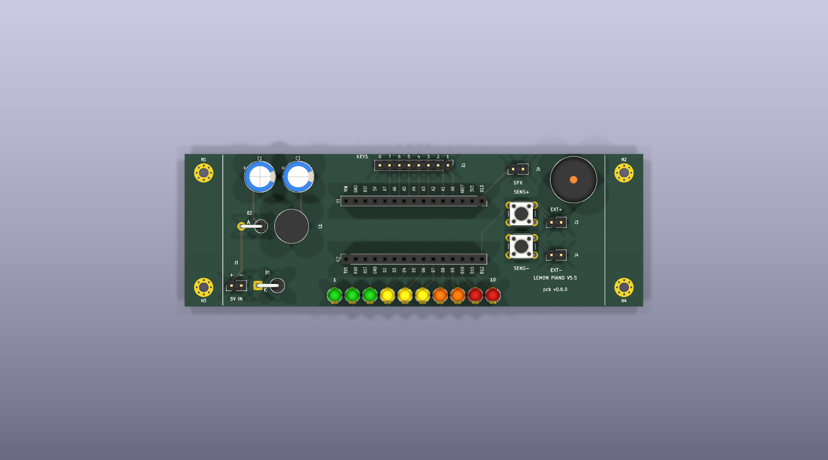
[picture p36: pcb/renders/v0.6.0-realistic-top.png]
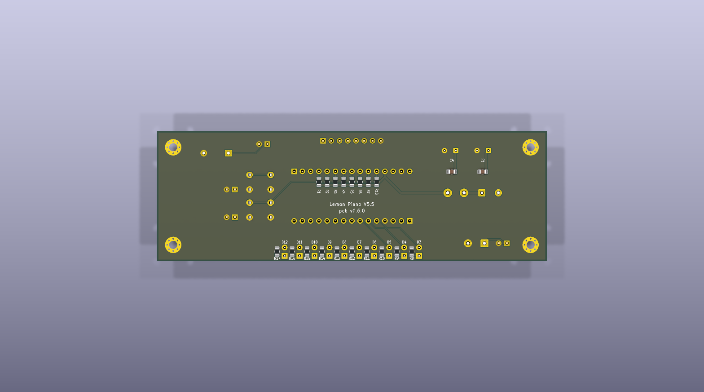
[picture p37: pcb/renders/v0.6.0-realistic-bottom.png]
v0.6.0 bottom
|  |  |

## v0.6.0 — overlay

| top | bottom |
|---|---|
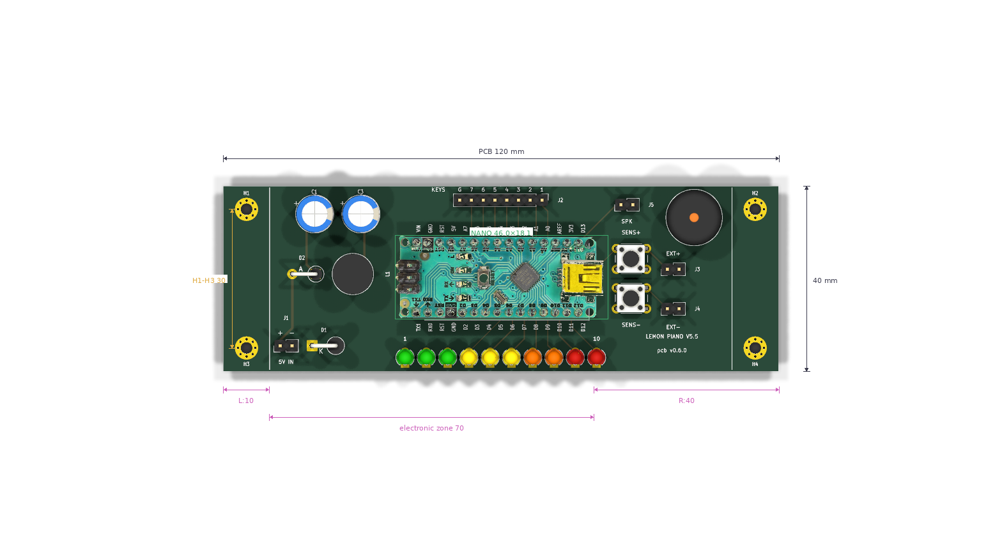
[picture p38: pcb/renders/v0.6.0-overlay-top.png]
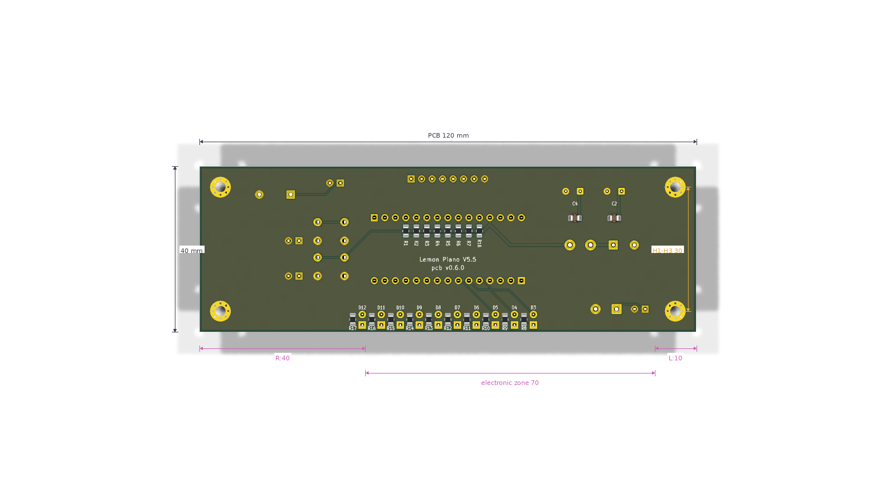
[picture p39: pcb/renders/v0.6.0-overlay-bottom.png]
v0.6.0 bottom
|  |  |

## v0.6.0 — normal

| top | bottom |
|---|---|
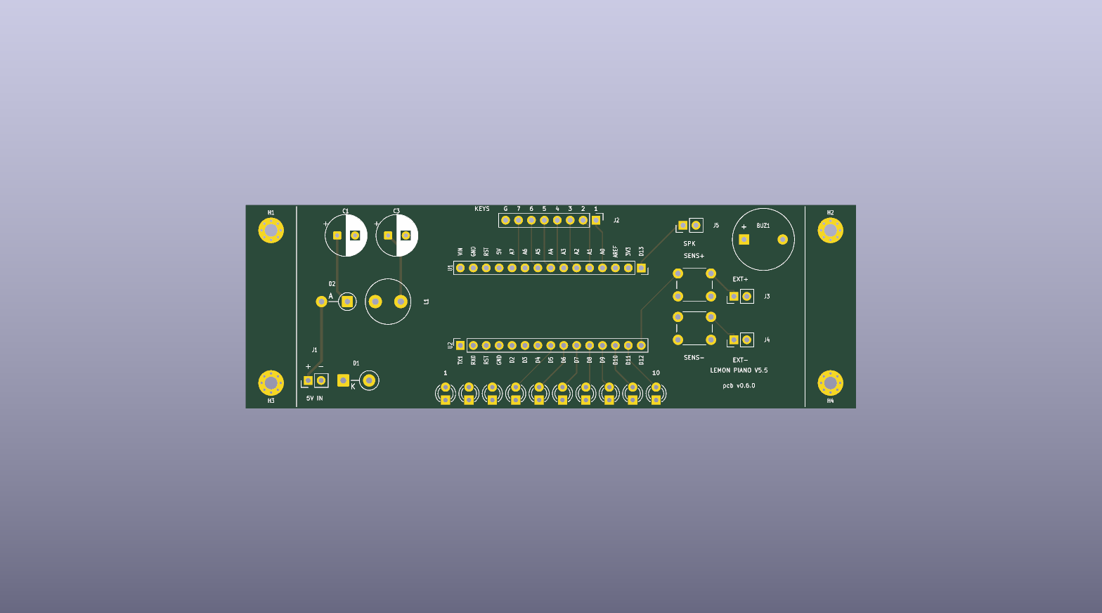
[picture p40: pcb/renders/v0.6.0-normal-top.png]
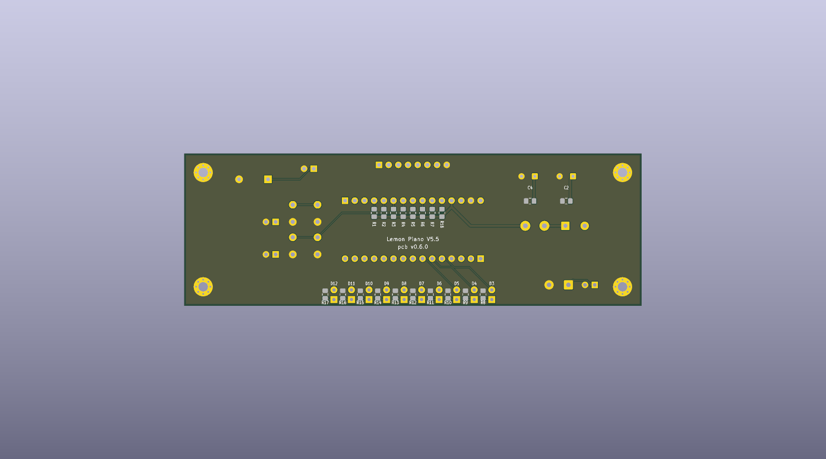
[picture p41: pcb/renders/v0.6.0-normal-bottom.png]
v0.6.0 bottom
|  |  |

## v0.6.0 — dim

| top | bottom |
|---|---|
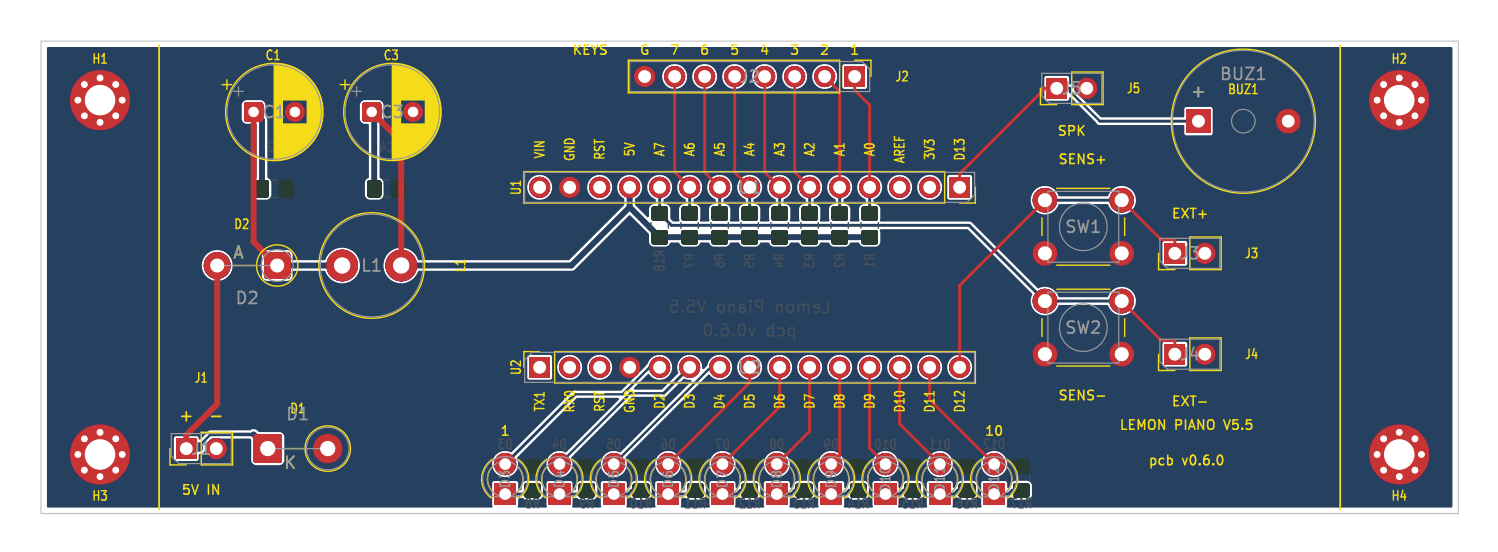
[picture p42: pcb/renders/v0.6.0-dim-top.png]
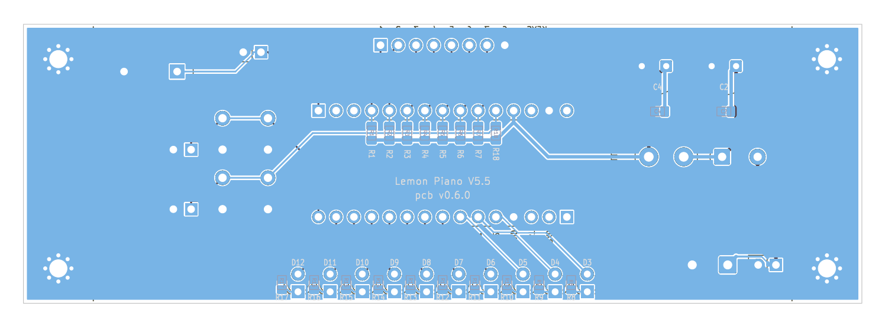
[picture p43: pcb/renders/v0.6.0-dim-bottom.png]
v0.6.0 bottom
|  |  |

## v0.5.1 — realistic

| top | bottom |
|---|---|
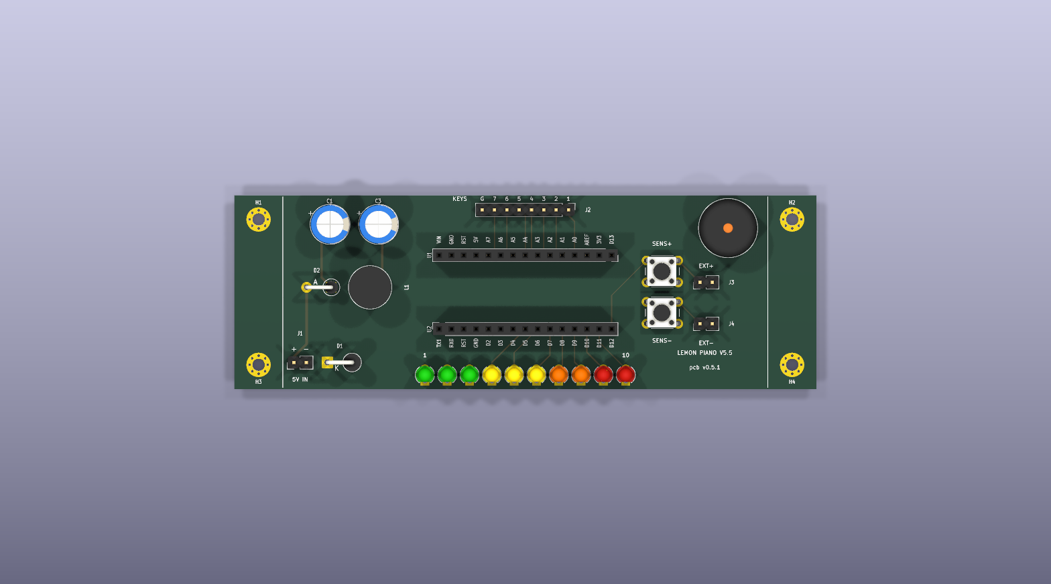
[picture p44: pcb/renders/v0.5.1-realistic-top.png]
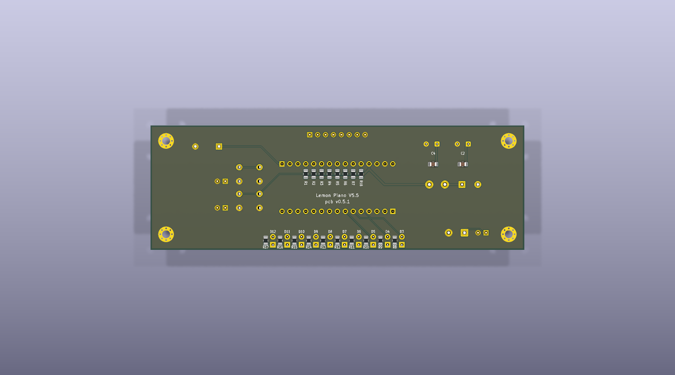
[picture p45: pcb/renders/v0.5.1-realistic-bottom.png]
v0.5.1 bottom
|  |  |

## v0.5.1 — overlay

| top | bottom |
|---|---|
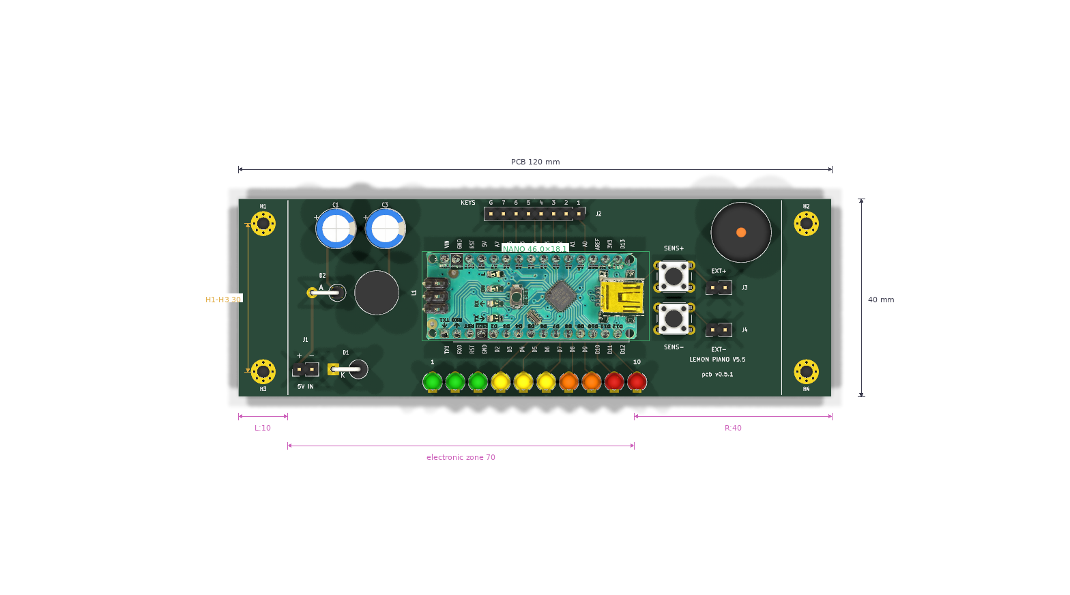
[picture p46: pcb/renders/v0.5.1-overlay-top.png]
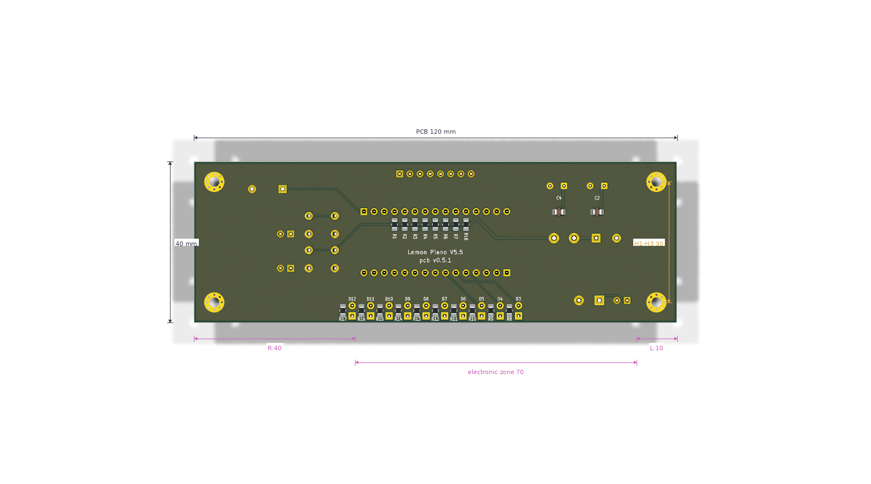
[picture p47: pcb/renders/v0.5.1-overlay-bottom.png]
v0.5.1 bottom
|  |  |

## v0.5.1 — normal

| top | bottom |
|---|---|
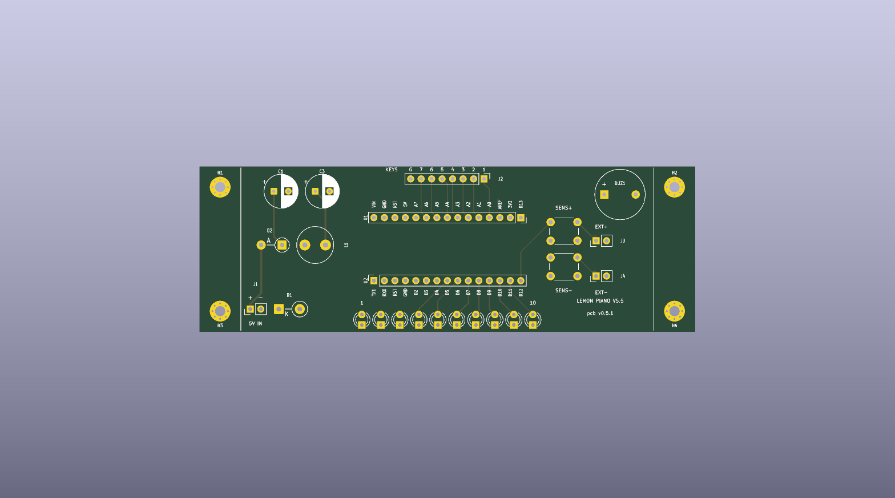
[picture p48: pcb/renders/v0.5.1-normal-top.png]
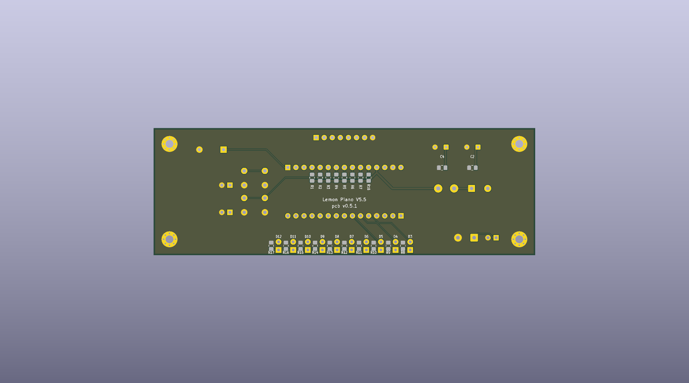
[picture p49: pcb/renders/v0.5.1-normal-bottom.png]
v0.5.1 bottom
|  |  |

## v0.5.1 — dim

| top | bottom |
|---|---|
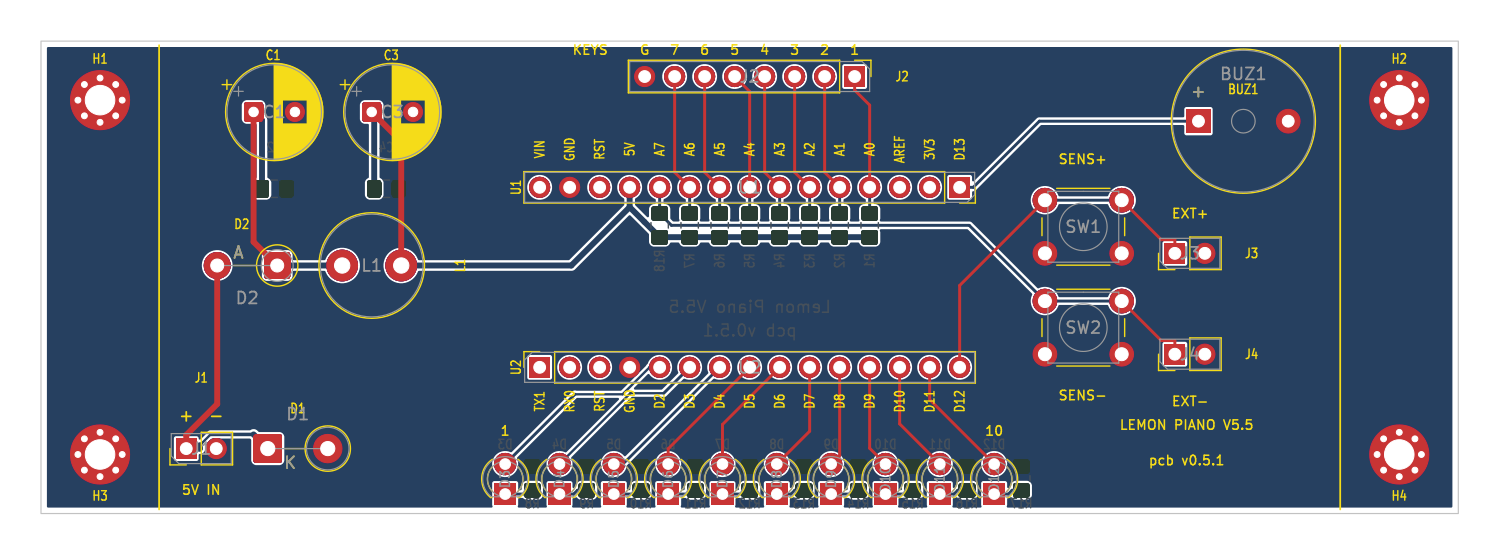
[picture p50: pcb/renders/v0.5.1-dim-top.png]
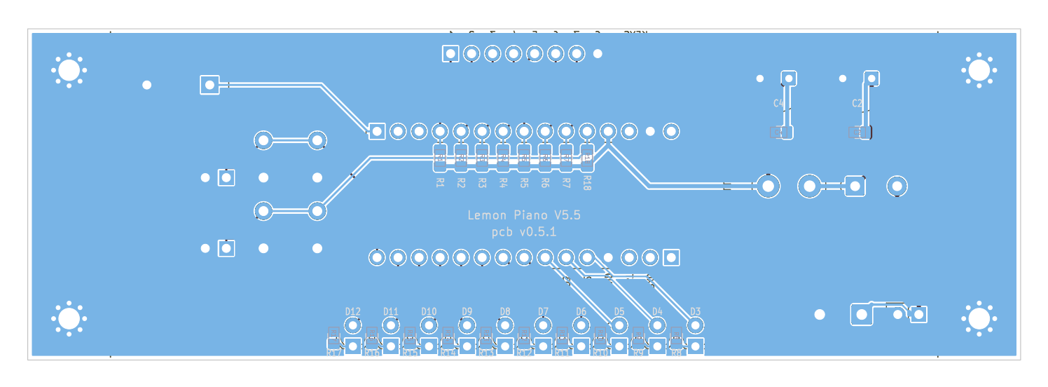
[picture p51: pcb/renders/v0.5.1-dim-bottom.png]
v0.5.1 bottom
|  |  |

## v0.5.0 — realistic

| top | bottom |
|---|---|
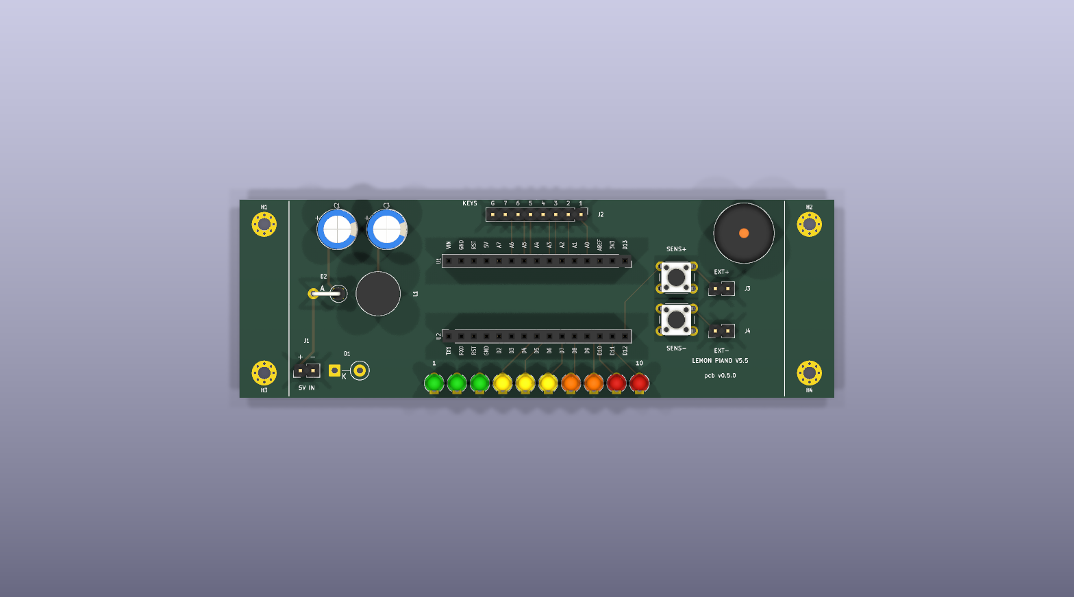
[picture p52: pcb/renders/v0.5.0-realistic-top.png]
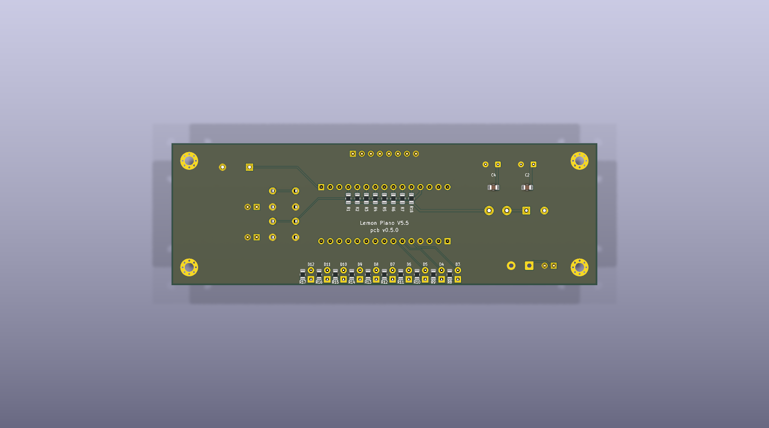
[picture p53: pcb/renders/v0.5.0-realistic-bottom.png]
v0.5.0 bottom
|  |  |

## v0.5.0 — overlay

| top | bottom |
|---|---|
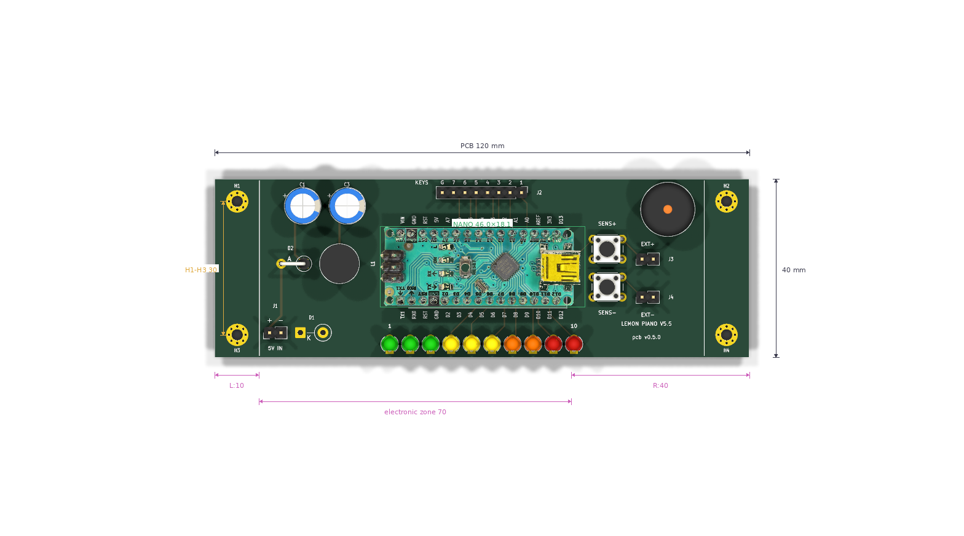
[picture p54: pcb/renders/v0.5.0-overlay-top.png]
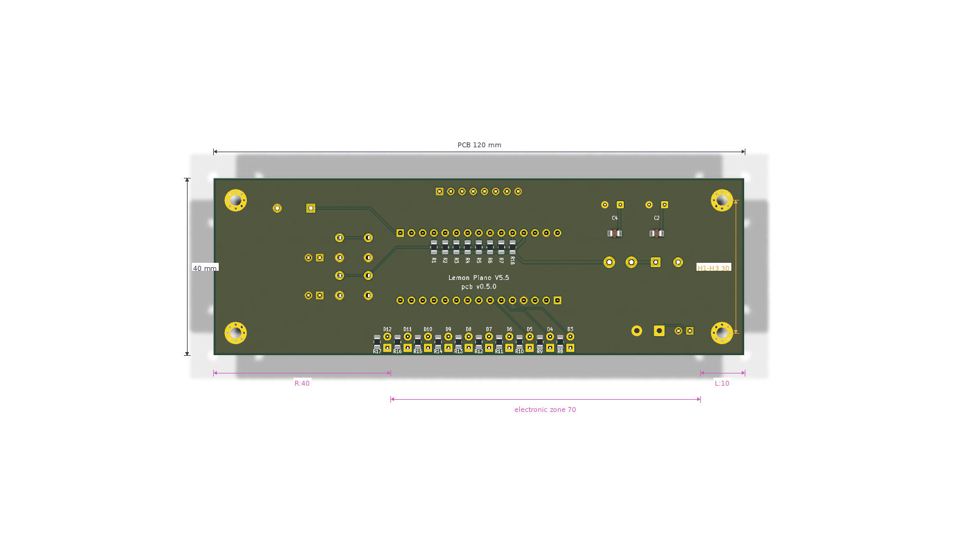
[picture p55: pcb/renders/v0.5.0-overlay-bottom.png]
v0.5.0 bottom
|  |  |

## v0.5.0 — normal

| top | bottom |
|---|---|
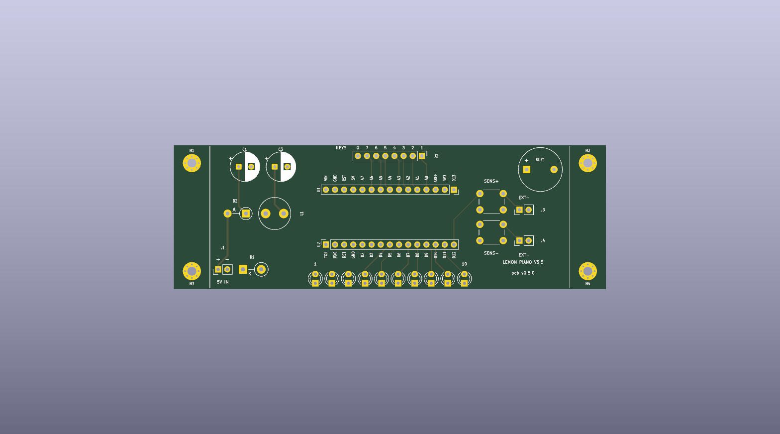
[picture p56: pcb/renders/v0.5.0-normal-top.png]
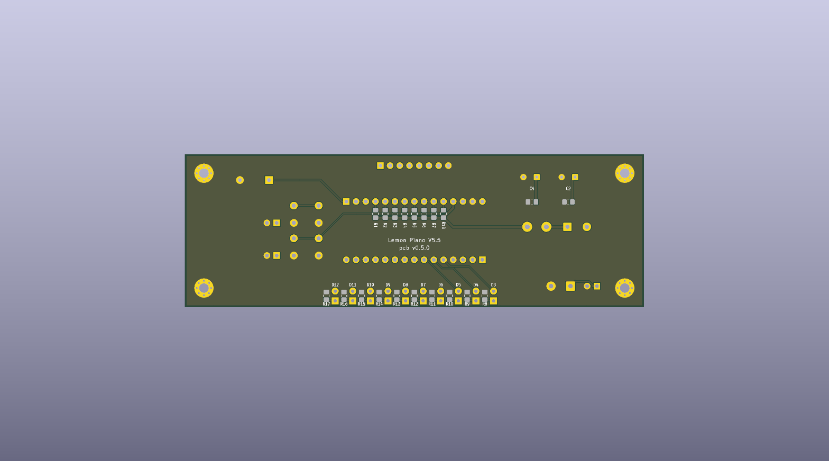
[picture p57: pcb/renders/v0.5.0-normal-bottom.png]
v0.5.0 bottom
|  |  |

## v0.5.0 — dim

| top | bottom |
|---|---|
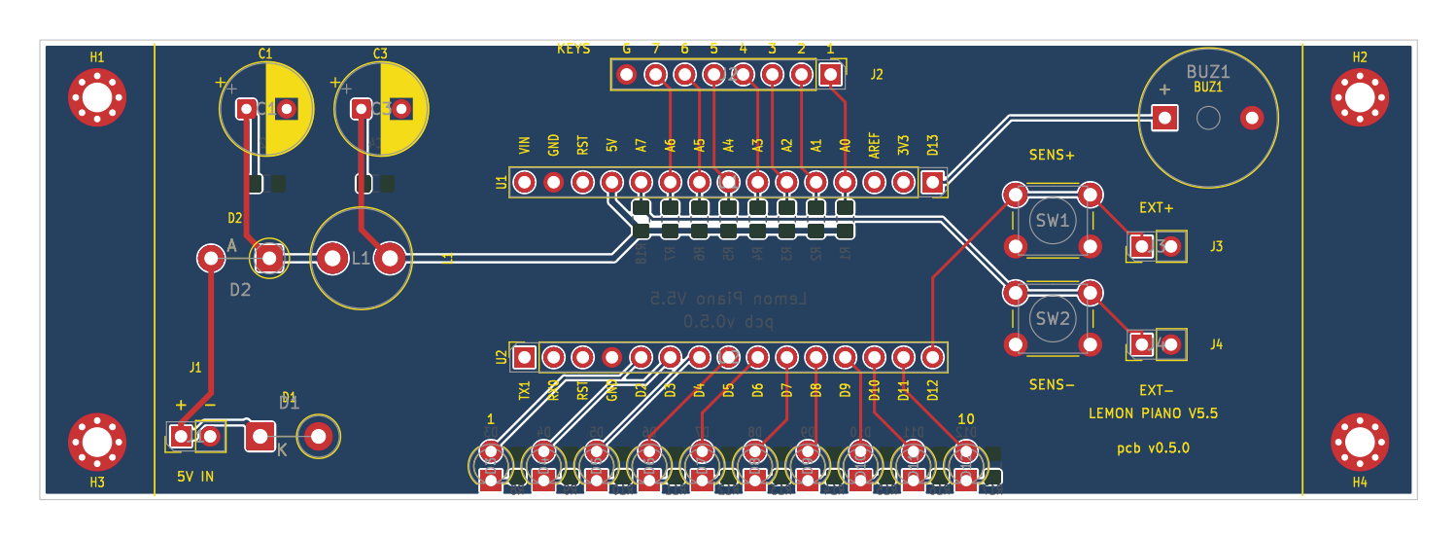
[picture p58: pcb/renders/v0.5.0-dim-top.png]
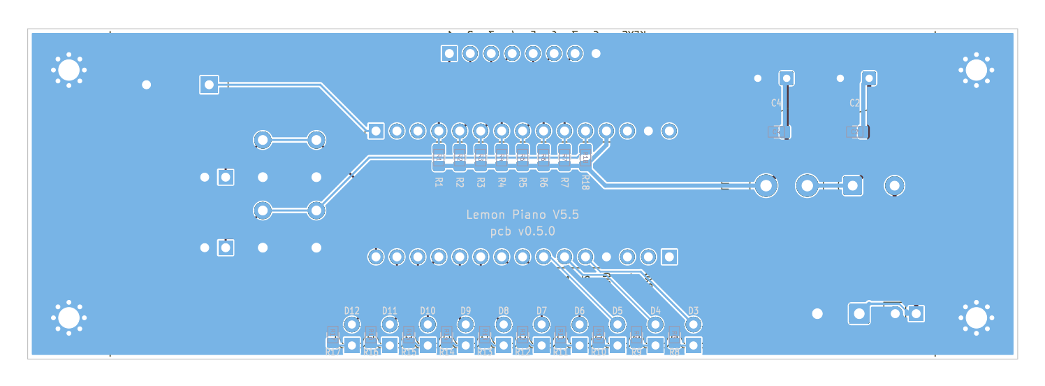
[picture p59: pcb/renders/v0.5.0-dim-bottom.png]
v0.5.0 bottom
|  |  |

## v0.4.0 — realistic

| top | bottom |
|---|---|
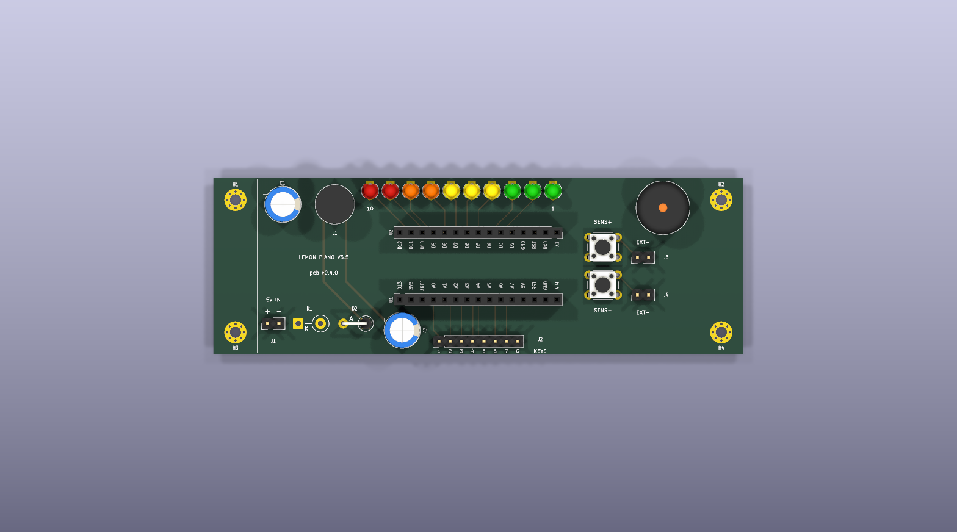
[picture p60: pcb/renders/v0.4.0-realistic-top.png]
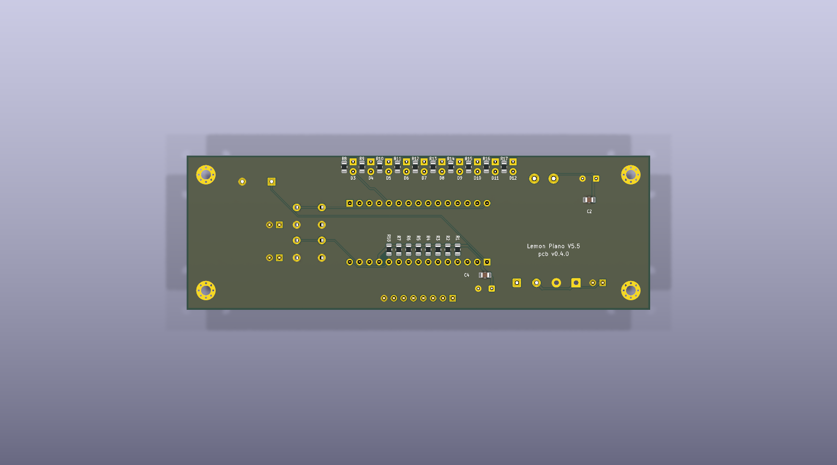
[picture p61: pcb/renders/v0.4.0-realistic-bottom.png]
v0.4.0 bottom
|  |  |

## v0.4.0 — overlay

| top | bottom |
|---|---|
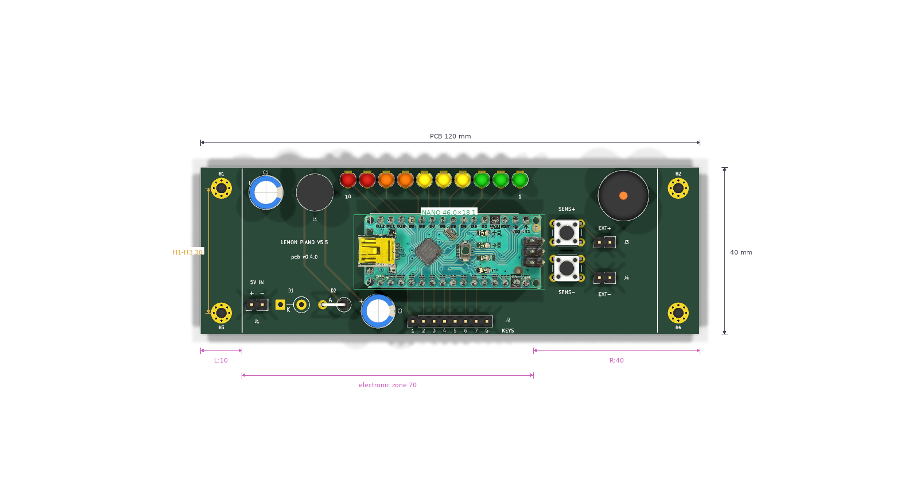
[picture p62: pcb/renders/v0.4.0-overlay-top.png]
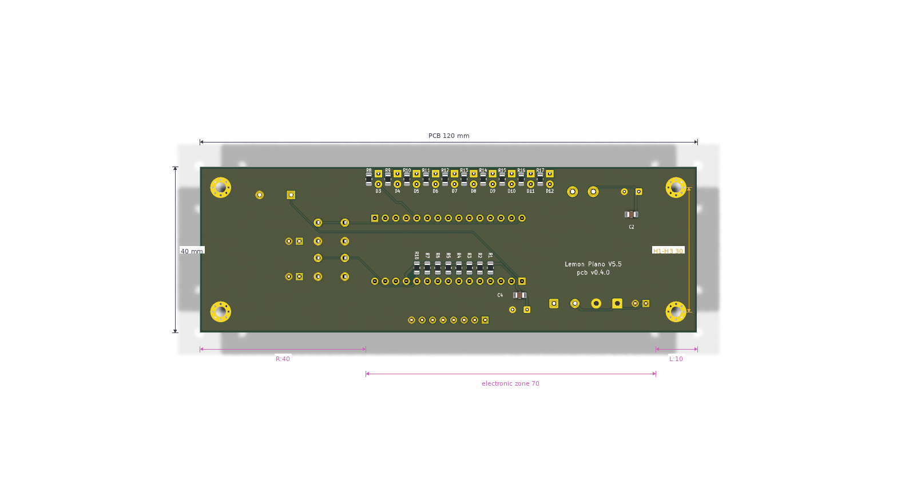
[picture p63: pcb/renders/v0.4.0-overlay-bottom.png]
v0.4.0 bottom
|  |  |

## v0.4.0 — normal

| top | bottom |
|---|---|
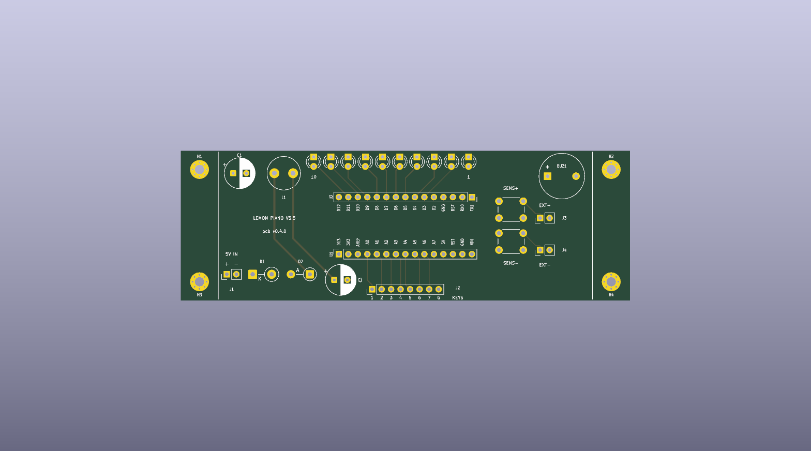
[picture p64: pcb/renders/v0.4.0-normal-top.png]
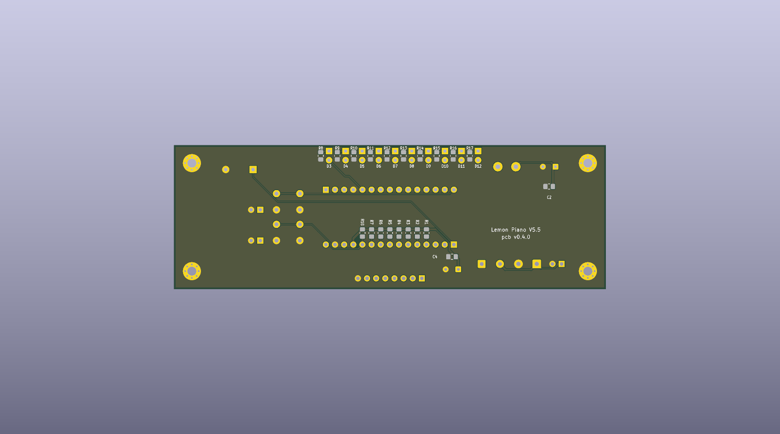
[picture p65: pcb/renders/v0.4.0-normal-bottom.png]
v0.4.0 bottom
|  |  |

## v0.4.0 — dim

| top | bottom |
|---|---|
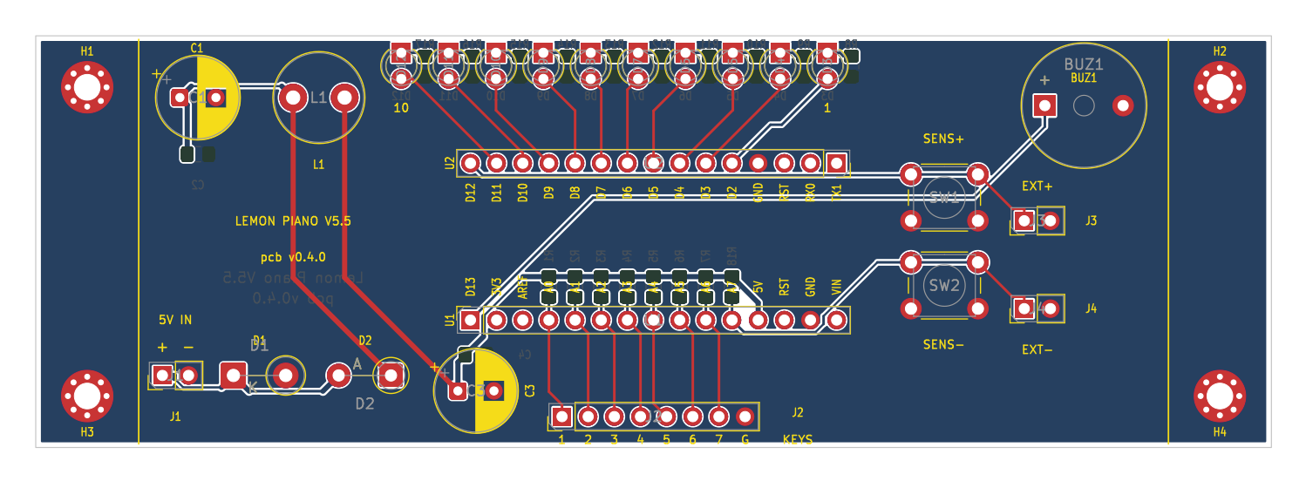
[picture p66: pcb/renders/v0.4.0-dim-top.png]
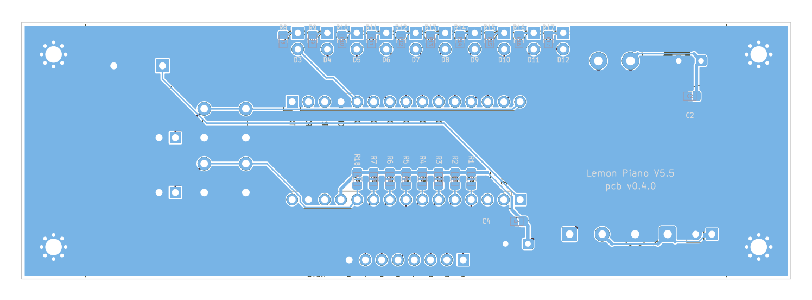
[picture p67: pcb/renders/v0.4.0-dim-bottom.png]
v0.4.0 bottom
|  |  |

## v0.3.0 — realistic

| top | bottom |
|---|---|
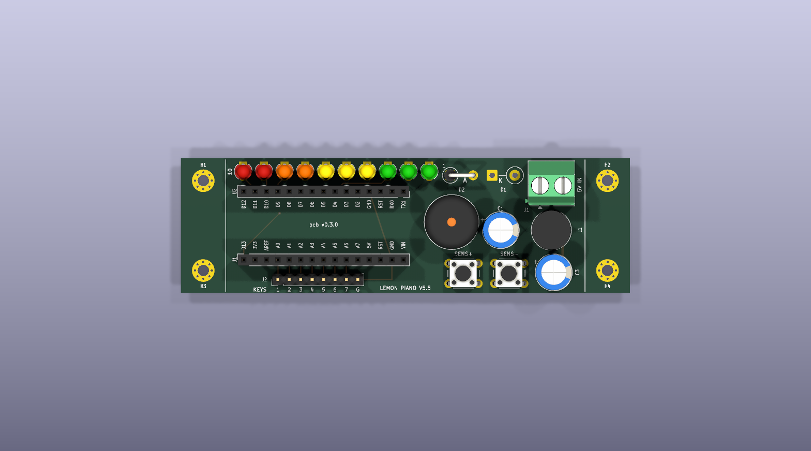
[picture p68: pcb/renders/v0.3.0-realistic-top.png]
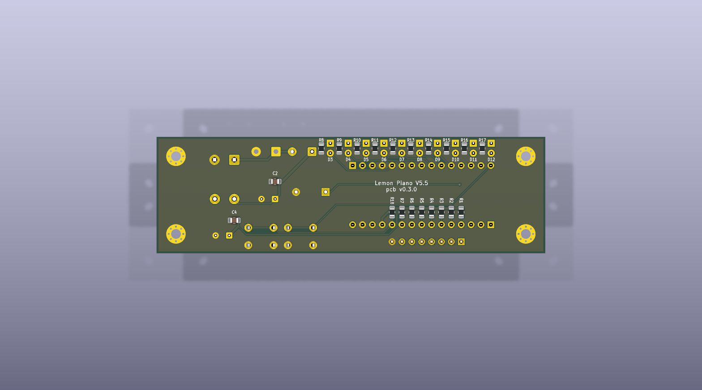
[picture p69: pcb/renders/v0.3.0-realistic-bottom.png]
v0.3.0 bottom
|  |  |

## v0.3.0 — overlay

| top | bottom |
|---|---|
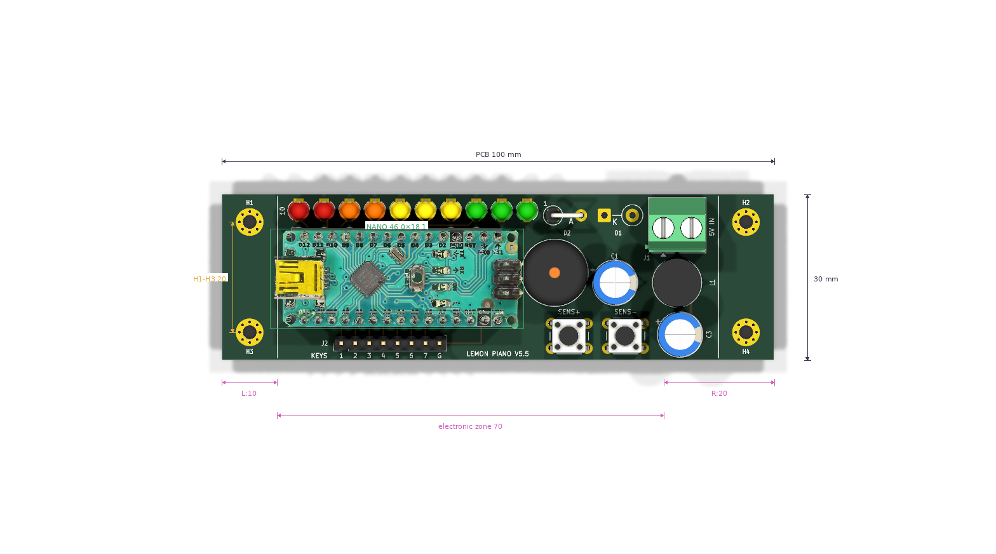
[picture p70: pcb/renders/v0.3.0-overlay-top.png]
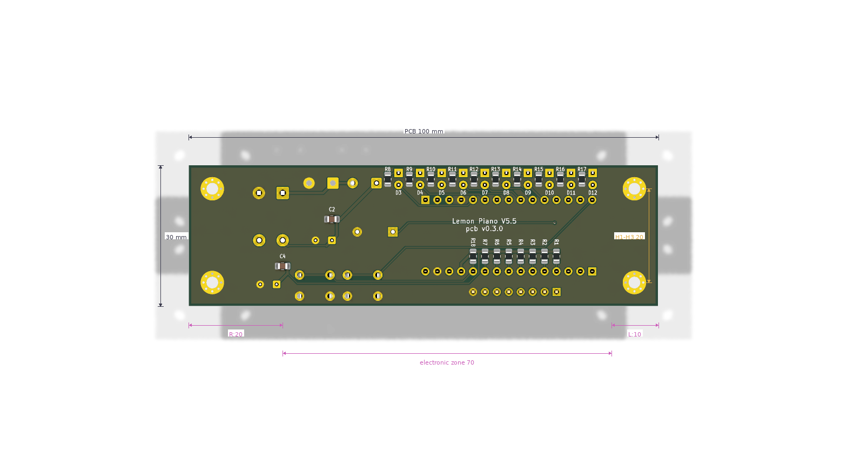
[picture p71: pcb/renders/v0.3.0-overlay-bottom.png]
v0.3.0 bottom
|  |  |

## v0.3.0 — normal

| top | bottom |
|---|---|
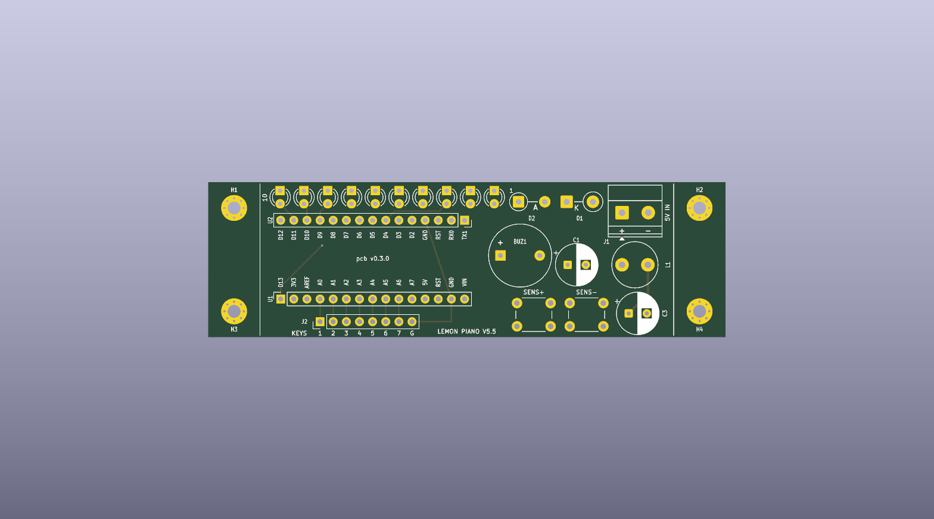
[picture p72: pcb/renders/v0.3.0-normal-top.png]
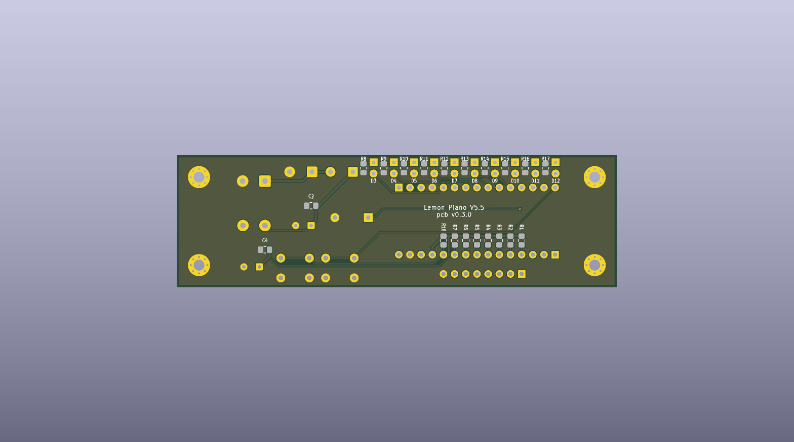
[picture p73: pcb/renders/v0.3.0-normal-bottom.png]
v0.3.0 bottom
|  |  |

## v0.3.0 — dim

| top | bottom |
|---|---|
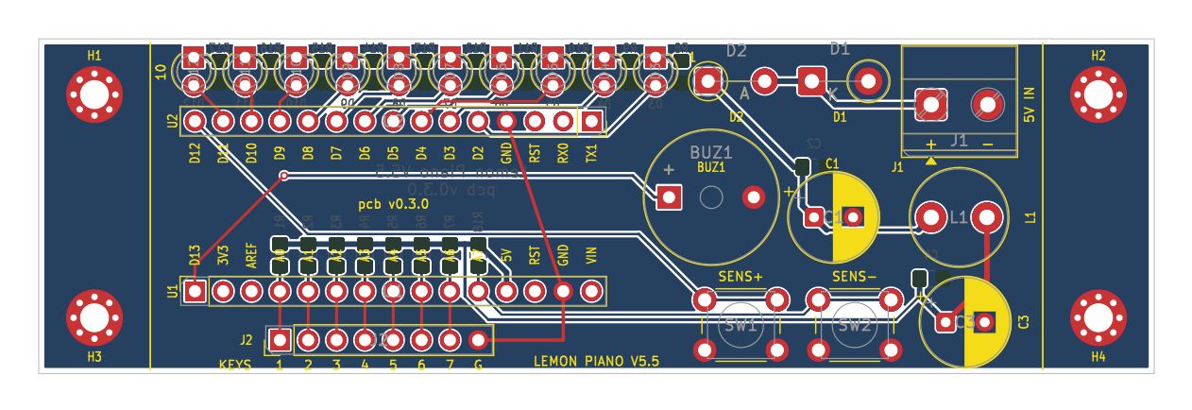
[picture p74: pcb/renders/v0.3.0-dim-top.png]
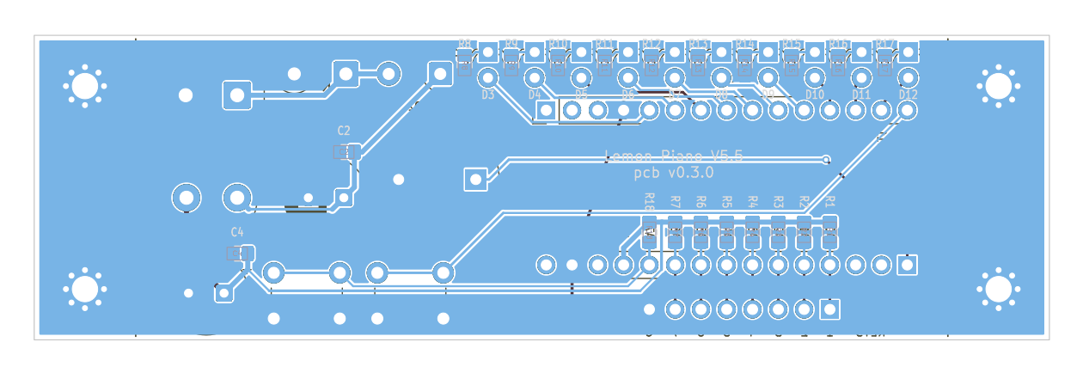
[picture p75: pcb/renders/v0.3.0-dim-bottom.png]
v0.3.0 bottom
|  |  |

## v0.2.1 — realistic

| top | bottom |
|---|---|
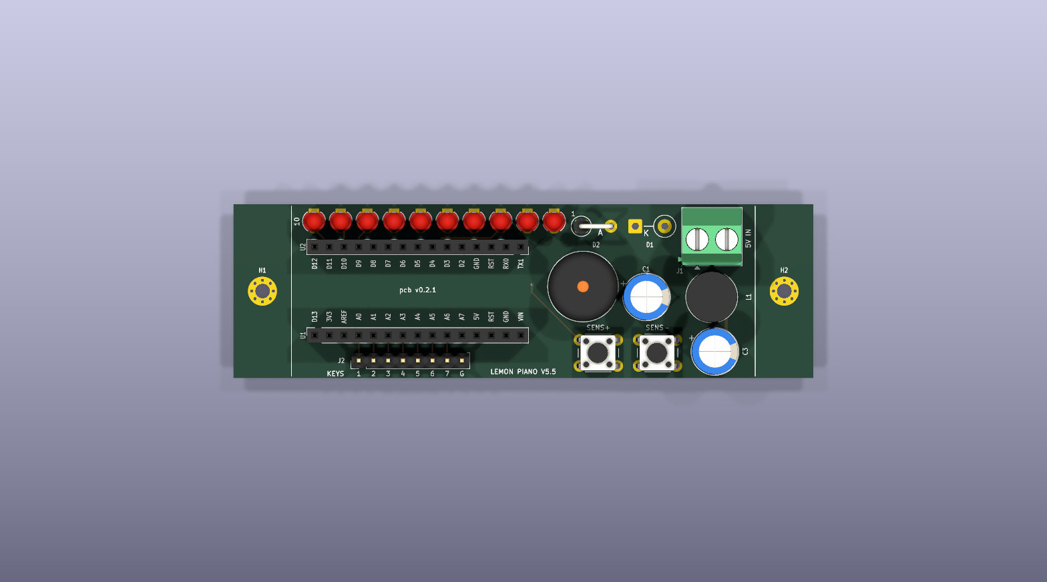
[picture p76: pcb/renders/v0.2.1-realistic-top.png]
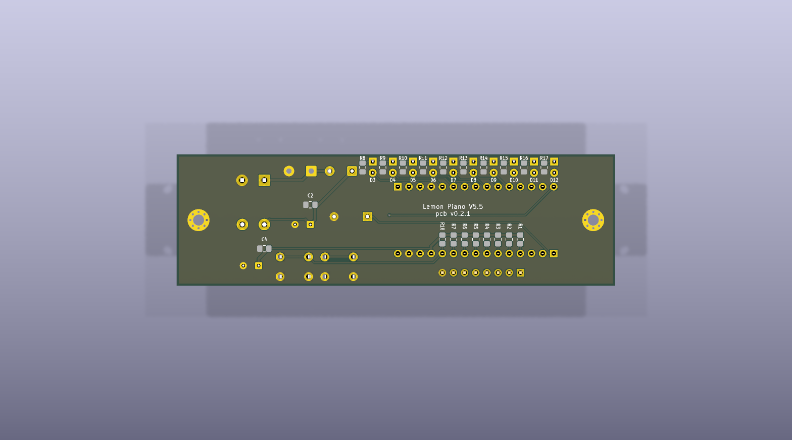
[picture p77: pcb/renders/v0.2.1-realistic-bottom.png]
v0.2.1 bottom
|  |  |

## v0.2.1 — overlay

| top | bottom |
|---|---|
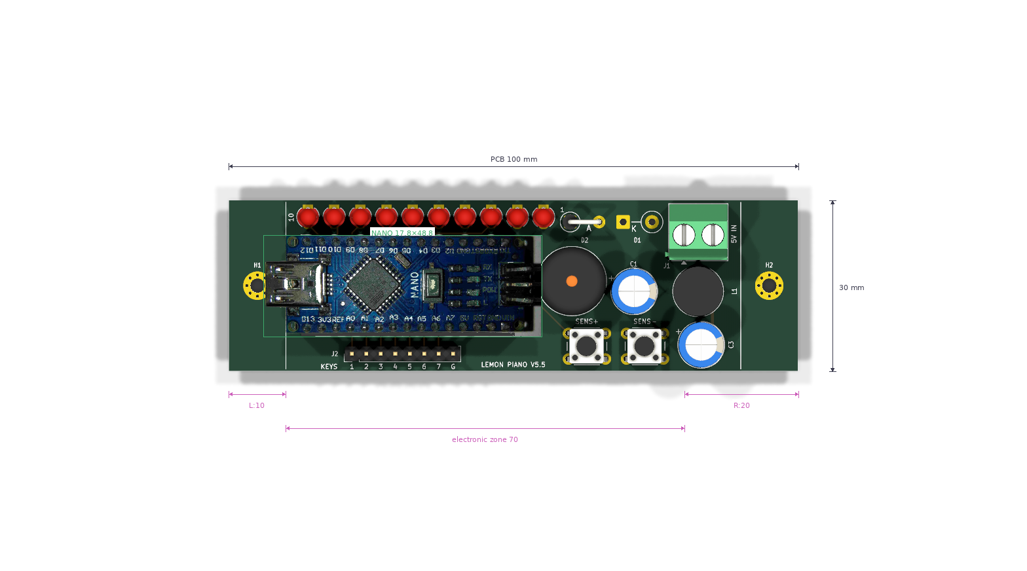
[picture p78: pcb/renders/v0.2.1-overlay-top.png]
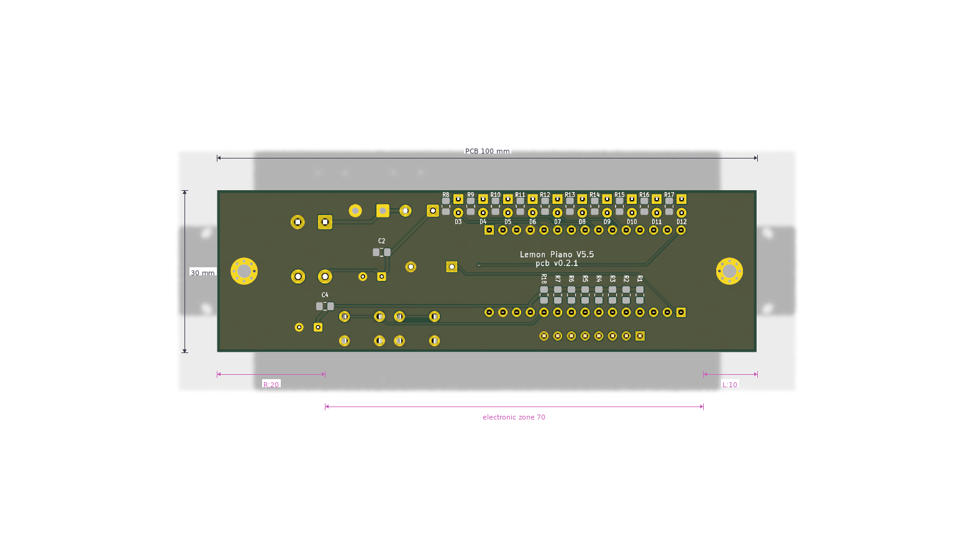
[picture p79: pcb/renders/v0.2.1-overlay-bottom.png]
v0.2.1 bottom
|  |  |

## v0.2.1 — normal

| top | bottom |
|---|---|
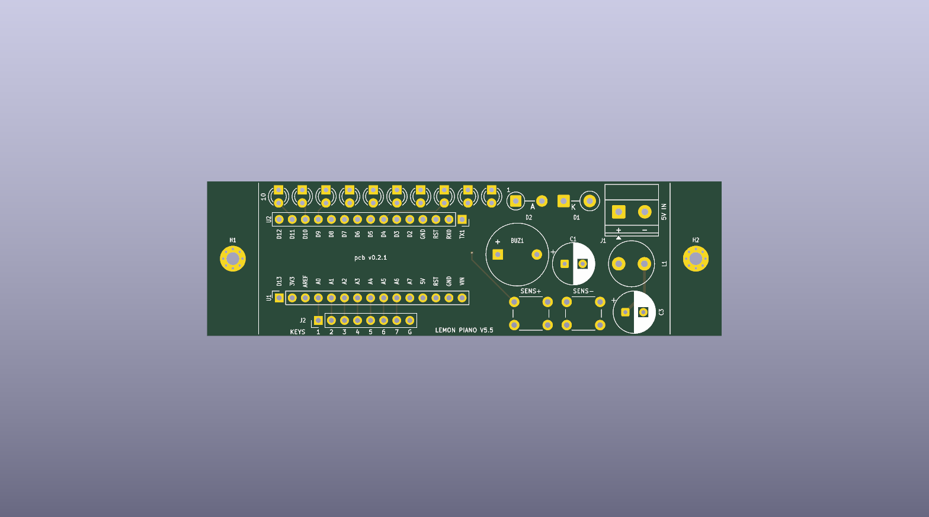
[picture p80: pcb/renders/v0.2.1-normal-top.png]
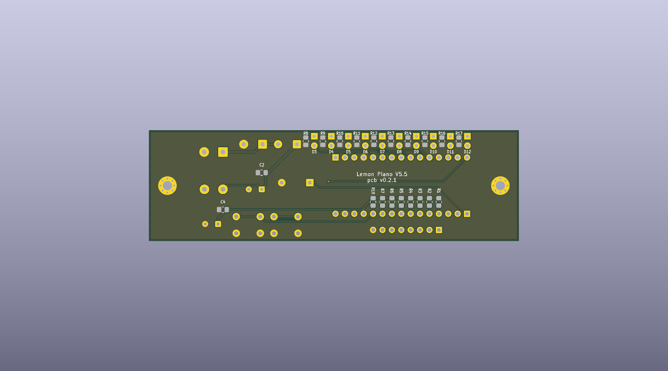
[picture p81: pcb/renders/v0.2.1-normal-bottom.png]
v0.2.1 bottom
|  |  |

## v0.2.1 — dim

| top | bottom |
|---|---|
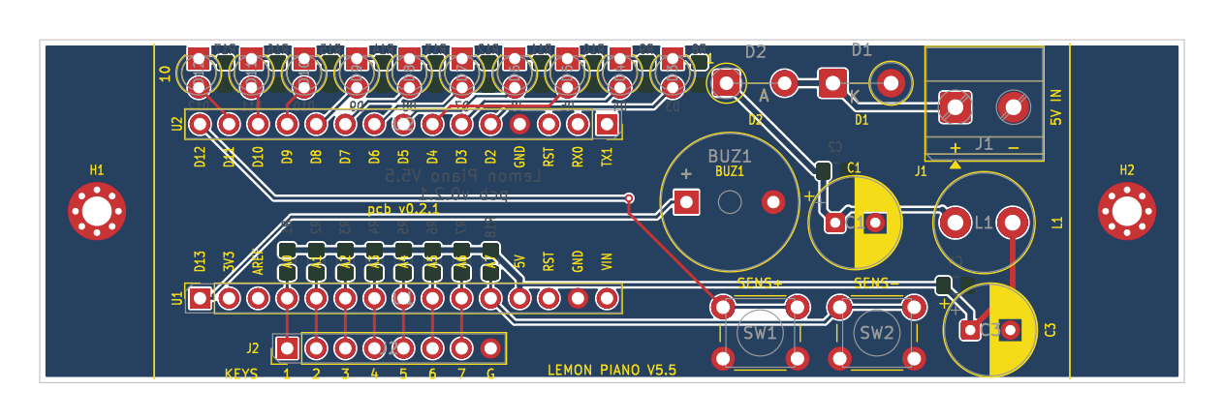
[picture p82: pcb/renders/v0.2.1-dim-top.png]
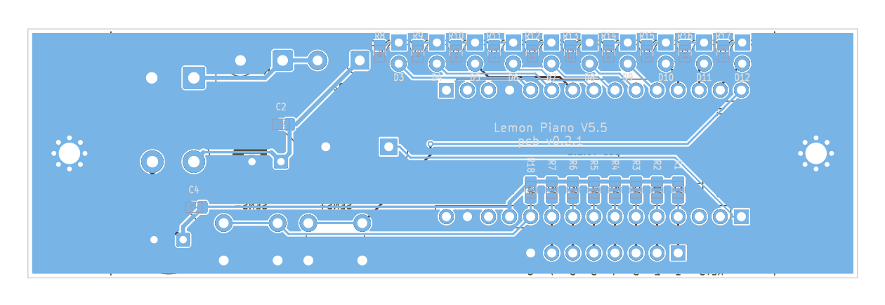
[picture p83: pcb/renders/v0.2.1-dim-bottom.png]
v0.2.1 bottom
|  |  |

## v0.2.0 — realistic

| top | bottom |
|---|---|
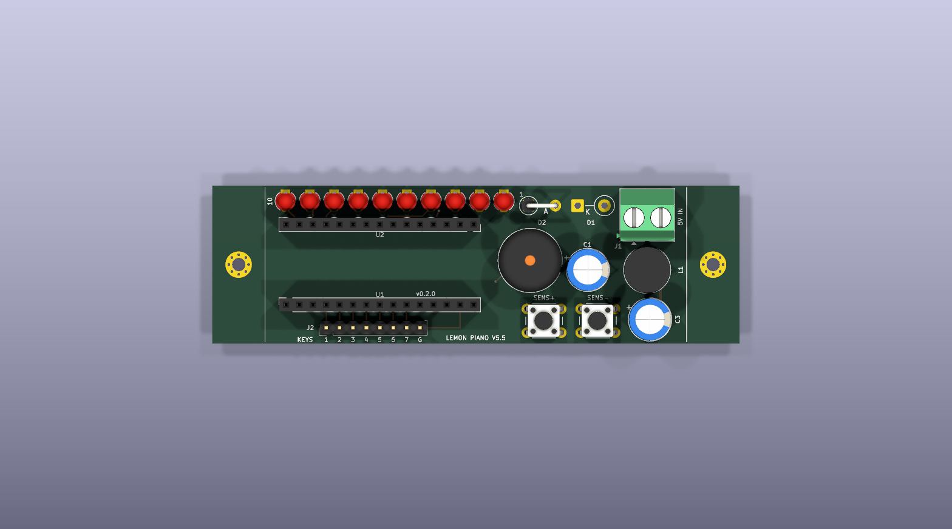
[picture p84: pcb/renders/v0.2.0-realistic-top.png]
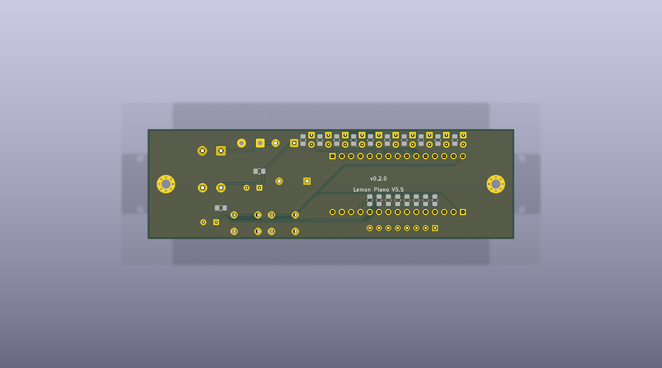
[picture p85: pcb/renders/v0.2.0-realistic-bottom.png]
v0.2.0 bottom
|  |  |

## v0.2.0 — overlay

| top | bottom |
|---|---|
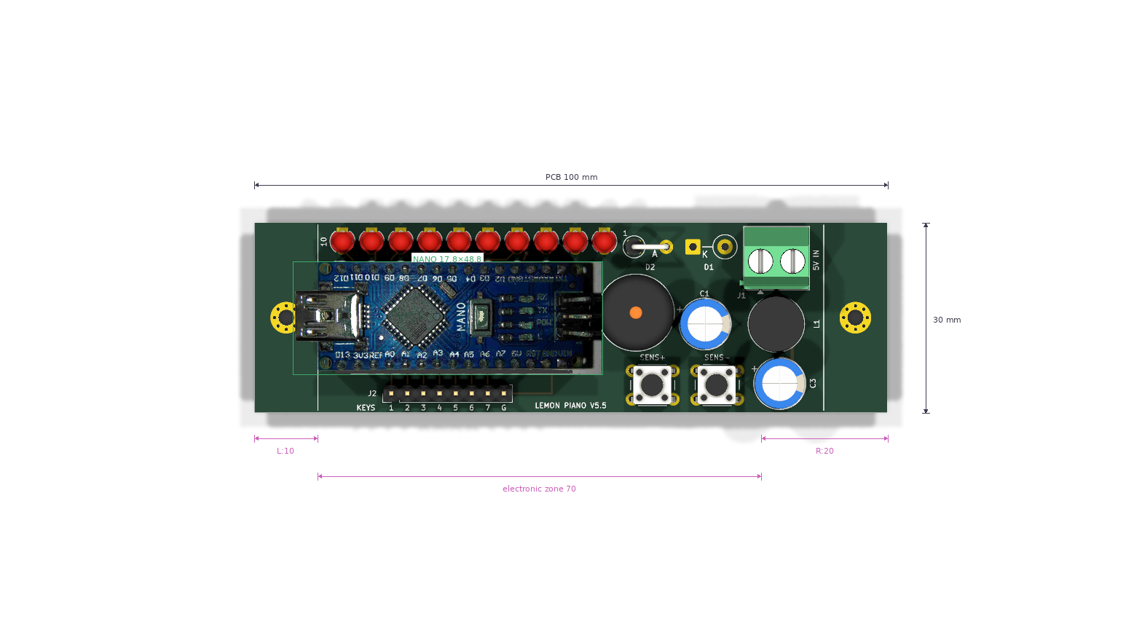
[picture p86: pcb/renders/v0.2.0-overlay-top.png]
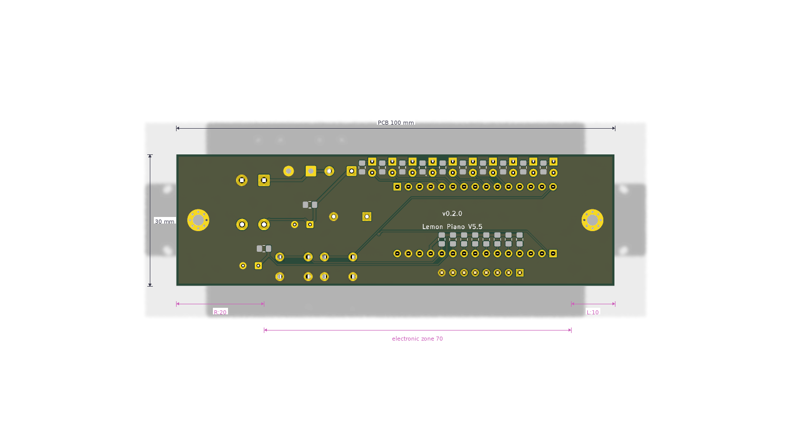
[picture p87: pcb/renders/v0.2.0-overlay-bottom.png]
v0.2.0 bottom
|  |  |

## v0.2.0 — normal

| top | bottom |
|---|---|
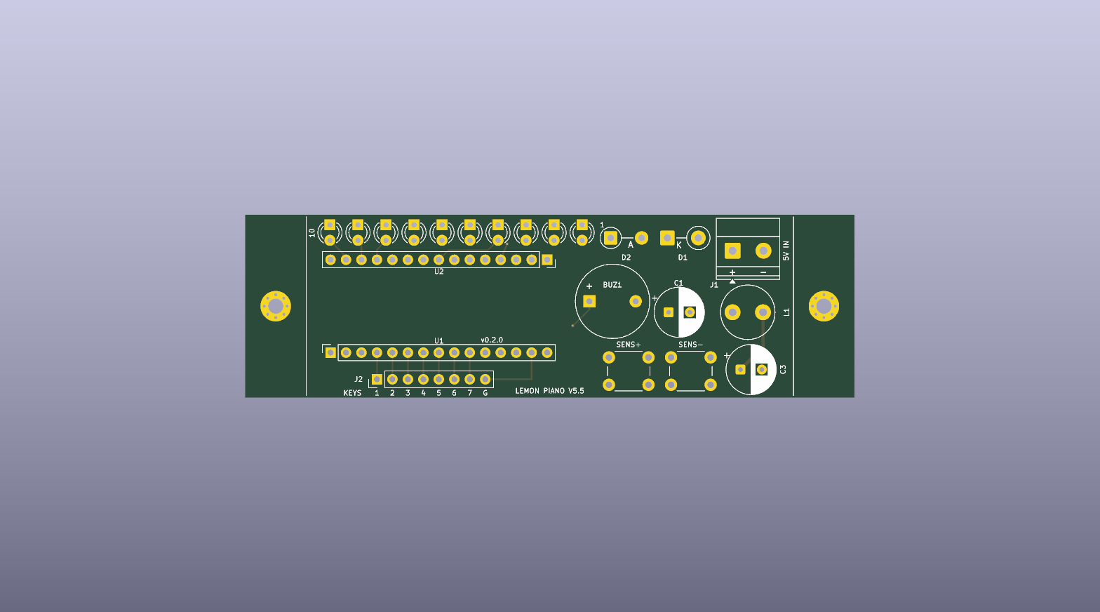
[picture p88: pcb/renders/v0.2.0-normal-top.png]
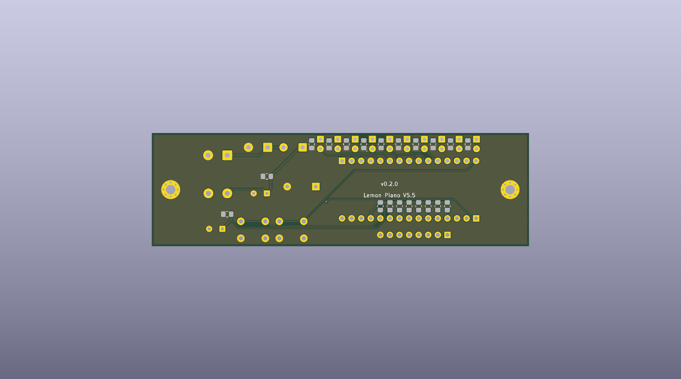
[picture p89: pcb/renders/v0.2.0-normal-bottom.png]
v0.2.0 bottom
|  |  |

## v0.2.0 — dim

| top | bottom |
|---|---|
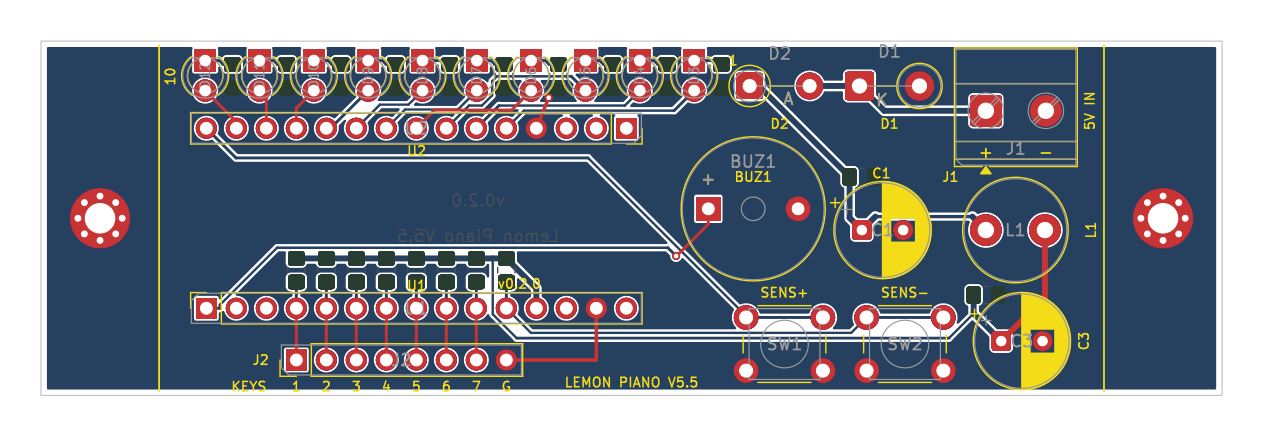
[picture p90: pcb/renders/v0.2.0-dim-top.png]
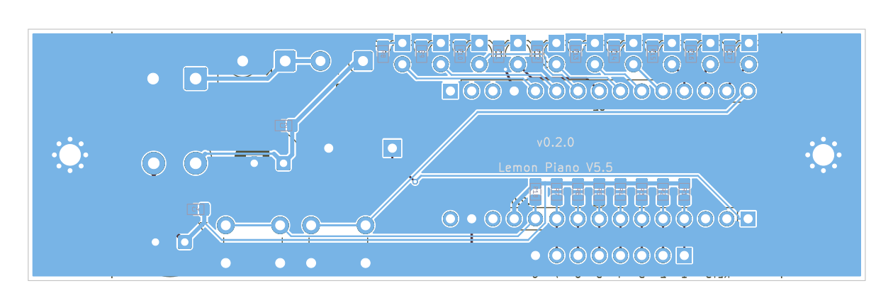
[picture p91: pcb/renders/v0.2.0-dim-bottom.png]
v0.2.0 bottom
|  |  |
