yupipi93/arduino-lemon-piano/docs/cartilla/cartilla.pdf

D O B L A A Q U Í

### LOS DOS BOTONES

+ | Más sensible. Enciende una luz más en la barra.
− | Menos sensible. Apaga una luz.

+ 3 SEG

MODO LIBRE ⇆ JUEGO. En modo libre los 7 limones son do re mi fa sol la si: no hay clave, ni fallos, ni nada que ganar.

− 3 SEG

Elegir nivel. Gira con + − y acepta pulsando LOS DOS A LA VEZ.

+ − 1 SEG Ajuste automático. Hazlo con el dedo puesto en un limón: mide ese dedo y se ajusta solo.

Al mantener un botón, la barra se va llenando y suena un pitido que sube: eso avisa de que va a cambiar algo. Suéltalo y no pasa nada.

### SI ALGO VA MAL

NO SUENA NADA

Comprueba que está enchufado. Al encender pita y recorre las luces: eso es que está calibrando.

MIENTRAS
CALIBRA

Nadie toca la fruta. Si alguien la toca mientras calibra, ese limón se queda mal ajustado.

SE DISPARA
SOLO

Toca − dos o tres veces.

NO COGE EL
DEDO

Toca + dos o tres veces. Y que apriete con toda la yema, no con la uña.

SE HACE UN LÍO Desenchufa y enchufa. Vuelve al nivel 1 y calibra de nuevo. No se rompe nada.

# PIANO

DE

# LIMONES

1 | 4 | 7

### G U ÍA D EL OR G A N IZA DOR

Para que cualquiera lo ponga en marcha y sepa explicarlo. Dentro están las 4 claves.

M U LT I T E C U A

### CÓMO SE JUEGA

7

TOCA LA FRUTA
7 limones = 7 notas. Hay que tocar el limón, no el cable.

Cada nivel esconde una clave de 10 notas. Las 10 luces son los 10 aciertos.

ACIERTO → se enciende una luz más.

FALLO → suena mal y se apagan TODAS. Se empieza la clave otra vez, desde el principio.

LAS 10 → suena la fanfarria y pasa solo al nivel siguiente.

### EL DEDO: LAS DOS DUDAS

### 1 NOTA

SI MANTIENE EL DEDO
Suena una sola nota, y dura todo el rato que aguante. Cuenta una vez. No pasa nada malo.

SI REPITE EL MISMO LIMÓN
Suena igual de bien, pero NO cuenta: una luz recorre la barra hacia atrás y el marcador se queda igual. No es un fallo y no quita nada. Para avanzar hay que tocar otro limón.

LO QUE SE OYE
Monedas, una por limón → está calibrando, manos fuera · Ruido corto y feo → nota equivocada · Fanfarria → nivel superado

### LAS 4 CLAVES

¿CUÁL ES EL LIMÓN 1? El que suena más grave; de ahí van subiendo hasta el 7. Para comprobarlo, mantén + 3 seg (modo libre) y tócalos en orden: do

NIVEL 1 | TEMA PRINCIPAL
6 | 5 | 6 | 7 | 2 | 5 | 2 | 1 | 3 | 4
NIVEL 2 | SUBSUELO
3 | 6 | 1 | 4 | 2 | 5 | 3 | 6 | 1 | 4
NIVEL 3 | | ESTRELLA
2 | 4 | 6 | 1 | 5 | 3 | 7 | 4 | 2 | 6
NIVEL 4 | | CASTILLO
5 | 1 | 3 | 7 | 2 | 6 | 4 | 1 | 5 | 3

El nivel se elige manteniendo − 3 seg. Cada nivel se anuncia con su propia música y enseña tantas luces como su número.
