yupipi93/arduino-lemon-piano/versions/v1-banana-piano/images/banana-piano-original.png

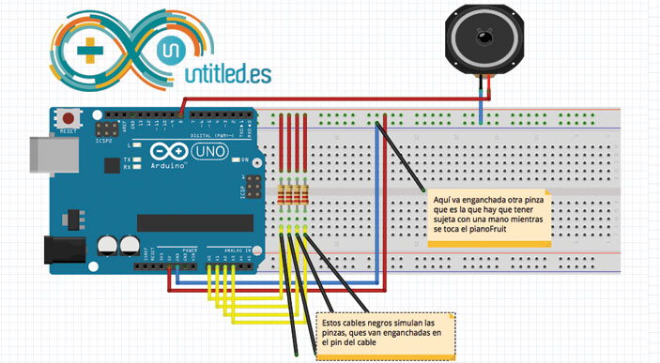
versions/v1-banana-piano/images/banana-piano-original.png
