yupipi93/arduino-lemon-piano/versions/v5.5-power-filter/model-design/enclosure-v6/renders/base-cavidad.png

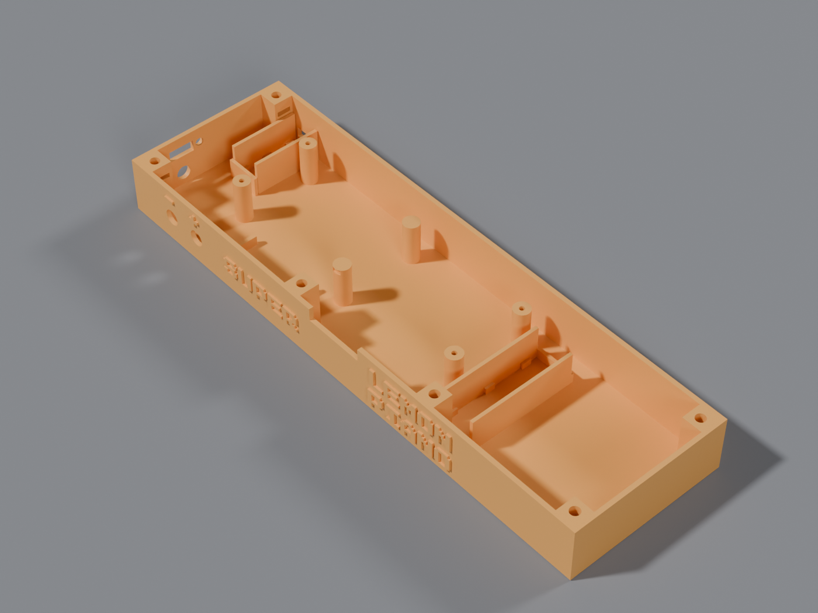
versions/v5.5-power-filter/model-design/enclosure-v6/renders/base-cavidad.png
