yupipi93/arduino-lemon-piano/versions/v5.5-power-filter/model-design/reference-images/amp-side.jpg

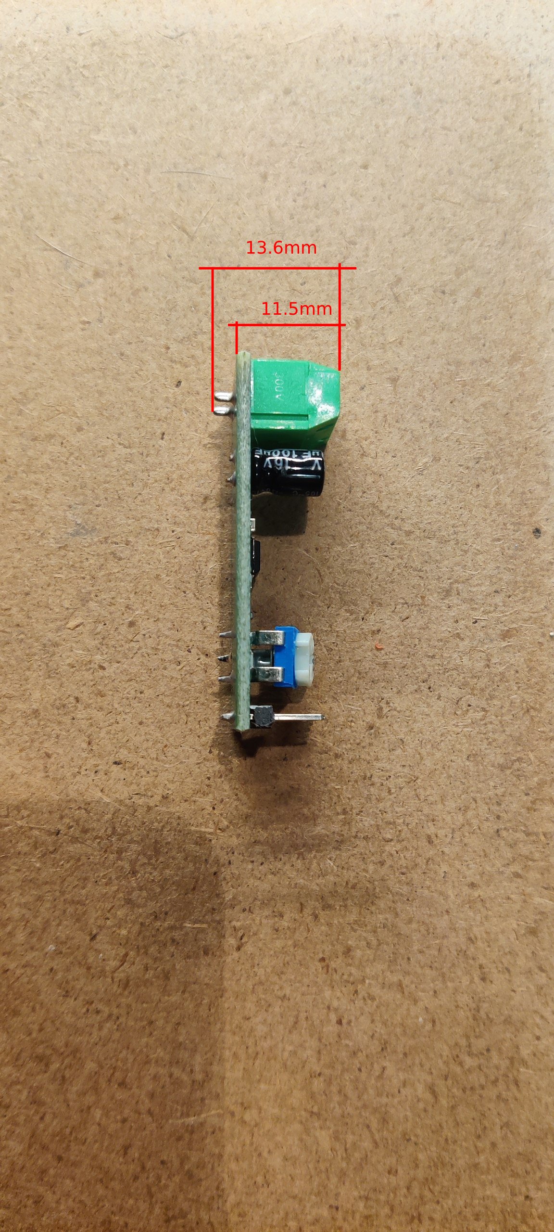
versions/v5.5-power-filter/model-design/reference-images/amp-side.jpg
