yupipi93/arduino-lemon-piano/pcb/overlays/component-images/arduino-nano.png

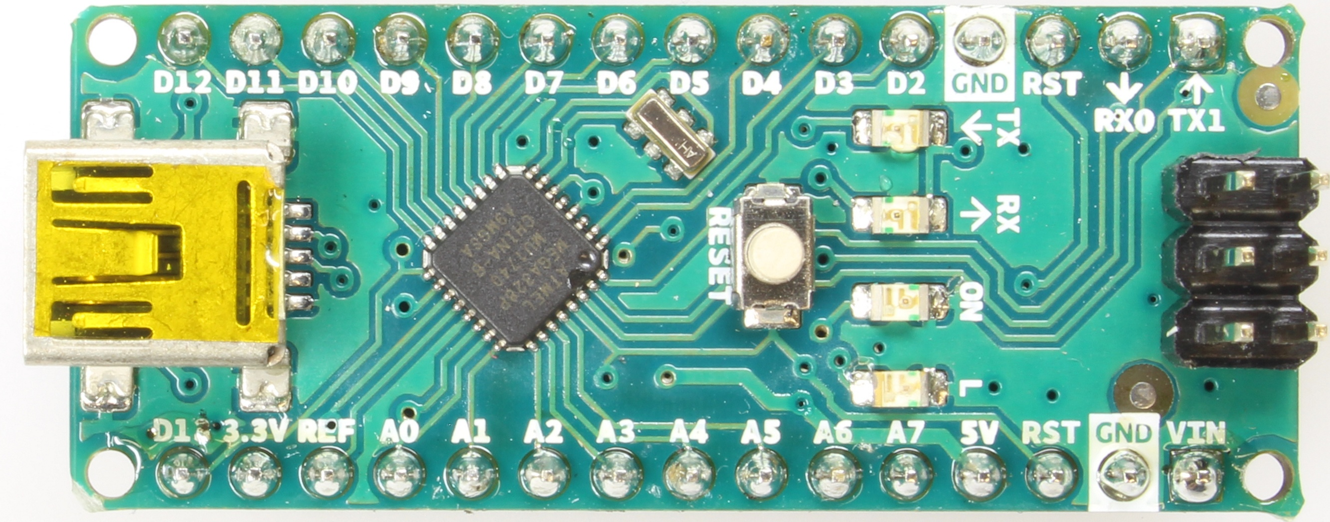
pcb/overlays/component-images/arduino-nano.png
