yupipi93/arduino-lemon-piano/pcb/validation/holes/holes-crops-bottom.png

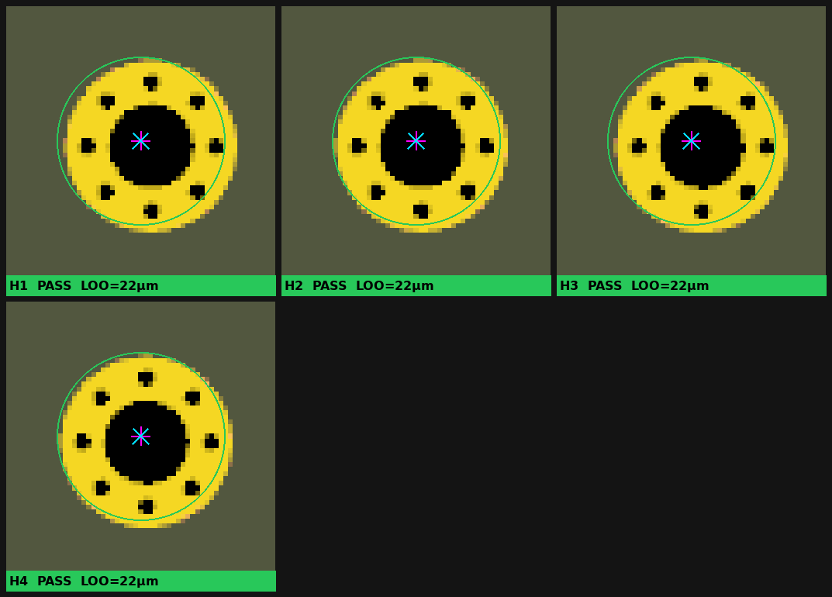
pcb/validation/holes/holes-crops-bottom.png
