yupipi93/arduino-lemon-piano/pcb/validation/holes/holes-crops-top.png

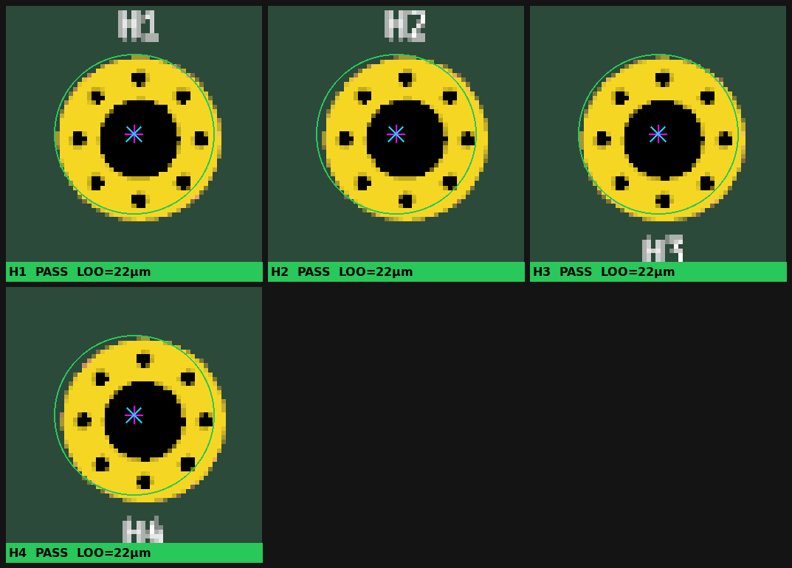
pcb/validation/holes/holes-crops-top.png
