yupipi93/arduino-lemon-piano/pcb/validation/holes/holes-diff-bottom.png

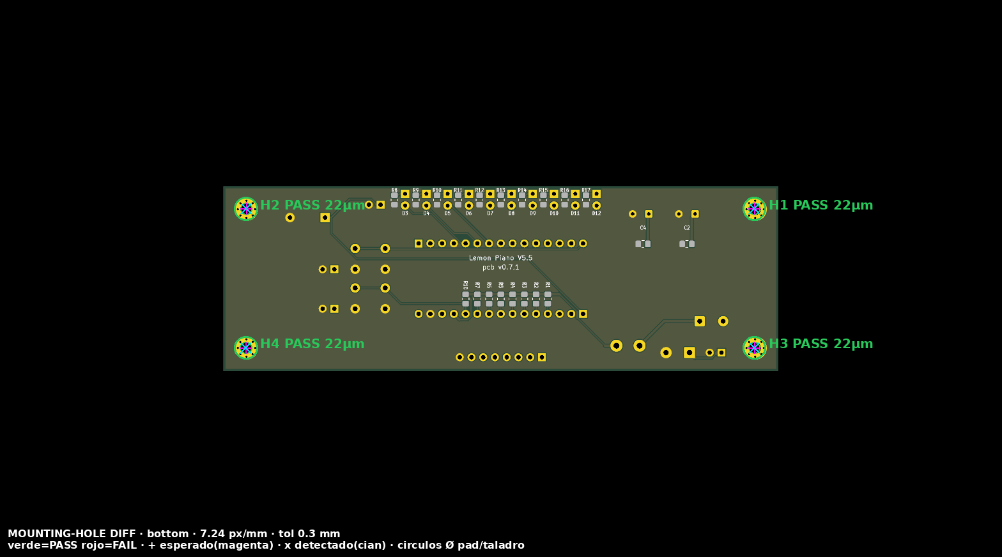
pcb/validation/holes/holes-diff-bottom.png
