yupipi93/arduino-lemon-piano/pcb/validation/holes/holes-diff-top.png

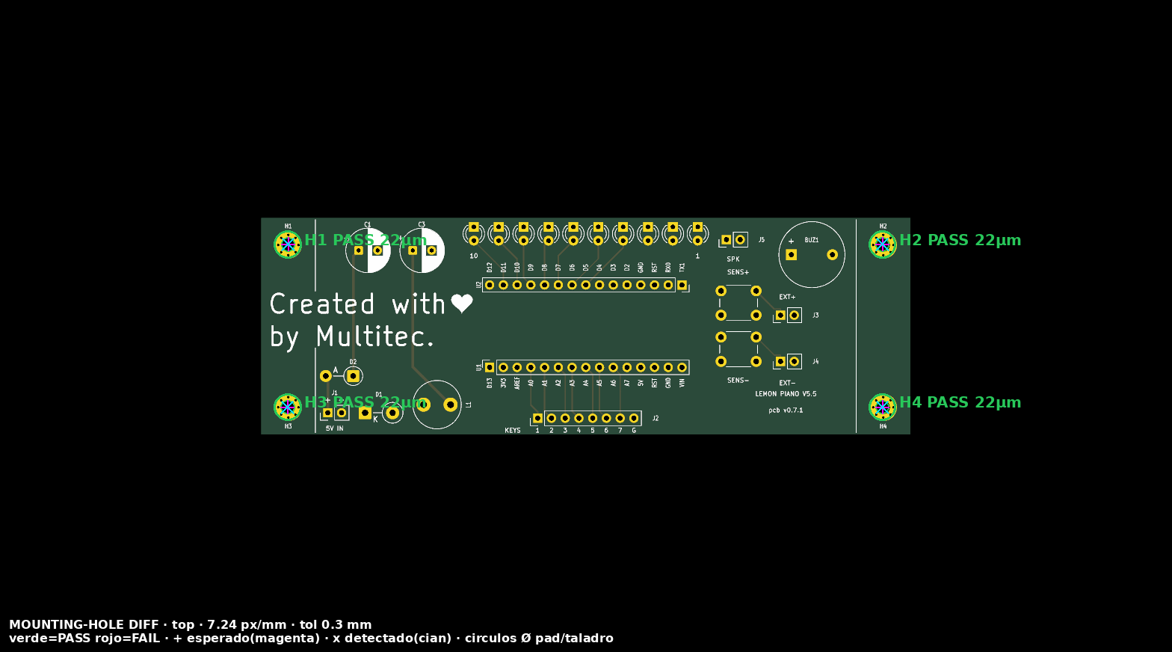
pcb/validation/holes/holes-diff-top.png
