yupipi93/arduino-lemon-piano/versions/v5.5-power-filter/firmware/test/arduino/Arduino.h

/* Arduino.h — a host stand-in for the AVR runtime, just big enough to run
 * src/main.cpp on a PC.
 *
 * WHY THIS EXISTS. The Velxio browser emulation cannot reach the mode wheel:
 * ten LEDs, a buzzer and key 7 already use every digital line, so there are no
 * pins left for the two buttons (see ../../emulation/README.md). And a piano
 * with a hidden menu is exactly the kind of thing that "compiles fine" and then
 * behaves wrongly in someone's hands. So the firmware gets driven end to end
 * HERE instead: real main.cpp, real melodies, real calibration, fake pins.
 *
 * It is a stand-in, not an emulator, and the difference matters when reading a
 * green result. Modelled: virtual time that advances the way the real chip's
 * does, seven analog touch channels with a baseline and noise, two buttons, ten
 * LEDs, and a log of every tone and every pin write. NOT modelled: interrupt
 * timing, Timer2, the ADC's actual behaviour, and anything electrical. It
 * proves the FIRMWARE'S LOGIC, and says nothing about the fruit.
 *
 * Time advances on delay(), delayMicroseconds(), and on every analogRead —
 * 112 us, the real conversion time — so a loop() that scans seven keys four
 * times over costs the ~3 ms it costs on the board, and gesture timings play
 * out at something close to their true rate rather than infinitely fast.
 */
#ifndef ARDUINO_SHIM_H
#define ARDUINO_SHIM_H

#include <stdint.h>
#include <stdio.h>
#include <string>
#include <vector>

// ── pins, in the Nano's numbering ───────────────────────────────────────────
#define A0 14
#define A1 15
#define A2 16
#define A3 17
#define A4 18
#define A5 19
#define A6 20
#define A7 21

#define HIGH 1
#define LOW 0
#define INPUT 0
#define OUTPUT 1
#define INPUT_PULLUP 2

#define PROGMEM
#define pgm_read_word(addr) (*(const int *) (addr))
#define pgm_read_byte(addr) (*(const uint8_t *) (addr))

class __FlashStringHelper;
#define F(str) ((const __FlashStringHelper *) (str))

// ── the fake machine ────────────────────────────────────────────────────────
struct FakeBoard {
  static const int PIN_COUNT = 32;
  static const int KEY_COUNT_ = 7;
  static const int ADC_TIME_US = 112;     // one real analogRead

  uint64_t micros_ = 0;

  int baseline[KEY_COUNT_];               // what an untouched channel reads
  int touchDepth = 8;                     // how far a finger drags it down
  bool touched[KEY_COUNT_];
  uint32_t noiseSeed = 12345;
  int noiseSpan = 2;                      // peak-to-peak idle wobble, in counts

  bool plusDown = false;                  // D12, active low
  bool minusDown = false;                 // A7, active low via a 10k pull-up

  uint8_t pinState[PIN_COUNT];
  uint8_t pinMode_[PIN_COUNT];

  // logs
  struct ToneEvent { int freq; uint32_t atMs; };
  std::vector<ToneEvent> tones;           // every tone() that started

  // ── the LED bar, as a FILM rather than a snapshot (2026-09-13) ───────────
  // Some of what this piano says is an ANIMATION, and an animation is invisible
  // to a test that only ever reads the final pin states: the backwards repeat
  // sweep starts and ends on the identical bar, which is the whole point of it.
  // So every change to the bar is appended here, one "#....." frame per change,
  // and a test can assert the shape of the motion in between.
  //
  // It is CAPPED. A long scenario writes the bar hundreds of times a second,
  // and an unbounded log ate the heap and segfaulted the runner before this cap
  // existed. Every reader works from a mark taken moments earlier, so only the
  // recent past is ever needed; when the cap is hit the oldest half is dropped
  // and `ledFramesDropped` records that it happened.
  static const size_t LED_FRAME_CAP = 40000;
  std::vector<std::string> ledFrames;
  size_t ledFramesDropped = 0;
  void pushLedFrame(const std::string &f) {
    if (ledFrames.size() >= LED_FRAME_CAP) {
      ledFrames.erase(ledFrames.begin(), ledFrames.begin() + LED_FRAME_CAP / 2);
      ledFramesDropped += LED_FRAME_CAP / 2;
    }
    ledFrames.push_back(f);
  }
  // ── every pin write, counted (2026-09-15) ───────────────────────────────
  // THE THEMES ARE BIT-BANGED. playSong() drives the buzzer pin by hand
  // (buzz(), in main.cpp) instead of going through tone(), because that is what
  // the 2019 code did and what the piezo is wired for — so `tones` above never
  // sees a single note of a level theme, and until now no test could tell
  // whether a tune had played at all. This counts raw writes per pin, which is
  // the only trace a bit-banged song leaves: pinWrites[BUZZER] after a theme is
  // twice its cycle count, and two playings of the SAME theme leave the same
  // number. That is what makes "it replayed the level's own music" assertable.
  unsigned long pinWrites[PIN_COUNT];

  std::string serial;
  bool traceSerial = false;

  FakeBoard() {
    for (int i = 0; i < KEY_COUNT_; i++) { baseline[i] = 1022; touched[i] = false; }
    for (int i = 0; i < PIN_COUNT; i++) { pinState[i] = LOW; pinMode_[i] = INPUT; pinWrites[i] = 0; }
  }

  uint32_t ms() const { return (uint32_t) (micros_ / 1000); }
  void advanceUs(uint64_t us) { micros_ += us; }

  int nextNoise() {                       // deterministic: the same run twice
    noiseSeed = noiseSeed * 1103515245u + 12345u;
    return (int) ((noiseSeed >> 16) % (uint32_t) (noiseSpan + 1));
  }
  // ── ADC settling on a high-impedance source (2026-09-13) ────────────────
  // A real ATmega's sample-and-hold cap charges through whatever is driving the
  // pin, and it starts each conversion holding the PREVIOUS channel's level.
  // How much of that gap one conversion closes depends on the source impedance:
  //
  //   220 Ohm  -> tau = 3 ns against a 12 us sampling window: instant (1.0)
  //   1 MOhm   -> tau = 14 us against the same window: 0.575 of the gap
  //
  // So on a 1 MOhm keyboard a single conversion is not a reading, it is a step
  // on the way to one, and readKey() must keep converting until the channel
  // stops moving. `adcSettle` is that fraction; 1.0 (the default) is the old
  // 220 Ohm board, where every other test lives and the bug cannot show.
  //
  // A7 (the SENS - button) is on the SAME multiplexer as the keys and is NOT
  // high impedance: a 10 kOhm pull-up, or a closed switch straight to GND. It
  // settles in one conversion and therefore poisons the keys without ever being
  // poisoned by them -- which is the whole asymmetry this models.
  static constexpr double SETTLE_1M = 0.575;
  double adcSettle = 1.0;
  double sampleHeld = 1023.0;             // what the S/H cap carries right now

  int convert(int target, double settle) {
    advanceUs(ADC_TIME_US);
    sampleHeld += settle * ((double) target - sampleHeld);
    return (int) (sampleHeld + 0.5);
  }

  // ── flaky fruit contact (2026-09-13) ────────────────────────────────────
  // A finger resting on a lemon is not a switch. Through 1 MOhm the contact
  // wanders, and the reading crosses back over the threshold for a few
  // milliseconds at a time without the finger going anywhere. Set
  // dropoutEveryMs/dropoutMs and a HELD key reads clear in bursts, which is
  // what made held fruit machine-gun itself before RELEASE_CONFIRM_MS.
  // Off by default: every other test wants a clean contact.
  uint32_t dropoutEveryMs = 0, dropoutMs = 0;
  bool contactBroken() const {
    if (dropoutEveryMs == 0) return false;
    return (uint32_t) ((micros_ / 1000) % dropoutEveryMs) < dropoutMs;
  }

  // ── coupling between channels (2026-09-15) ──────────────────────────────
  // The lemons sit in a row, touching each other, and the player is the return
  // path for all of them: one finger on one lemon already drags the OTHER
  // channels part of the way down. That is why strongestKey() picks a winner by
  // depth instead of taking the first channel over its threshold — and it is
  // the entire difficulty of telling "two fingers" from "one finger and its
  // shadows" (chordPartnerFor() in main.cpp).
  //
  // A ghost dips by couplingDepth, a finger by touchDepth. Zero by default, so
  // every test written before this one sees the clean board it was written for;
  // the chord tests set it and are the reason it exists.
  int couplingDepth = 0;
  bool anyTouched() const {
    for (int i = 0; i < KEY_COUNT_; i++) if (touched[i]) return true;
    return false;
  }

  int settledValue(int k) {
    int v = baseline[k] - nextNoise();
    if (touched[k] && !contactBroken()) v -= touchDepth;
    else if (couplingDepth > 0 && !contactBroken() && anyTouched()) v -= couplingDepth;
    return v < 0 ? 0 : v;
  }
  // Called on every pin change; records a frame only when it was a bar LED.
  void noteLedFrame(uint8_t pin);

  int readChannel(int k)      { return convert(settledValue(k), adcSettle); }
  int readButtonChannel()     { return convert(minusDown ? 0 : 1023, 1.0); }
};

extern FakeBoard board;

// ── the API main.cpp actually uses ──────────────────────────────────────────
inline unsigned long millis() { return board.ms(); }
inline unsigned long micros() { return (unsigned long) board.micros_; }
inline void delay(unsigned long ms) { board.advanceUs((uint64_t) ms * 1000); }
inline void delayMicroseconds(unsigned int us) { board.advanceUs(us); }

inline void pinMode(uint8_t pin, uint8_t mode) {
  if (pin < FakeBoard::PIN_COUNT) board.pinMode_[pin] = mode;
}
inline void digitalWrite(uint8_t pin, uint8_t v) {
  if (pin >= FakeBoard::PIN_COUNT) return;
  board.pinWrites[pin]++;
  const uint8_t was = board.pinState[pin];
  board.pinState[pin] = v;
  if (was != v) board.noteLedFrame(pin);
}
inline int digitalRead(uint8_t pin) {
  if (pin == 12) return board.plusDown ? LOW : HIGH;   // SENS_UP, to GND
  return board.pinState[pin];
}
inline int analogRead(uint8_t pin) {
  if (pin < FakeBoard::KEY_COUNT_) return board.readChannel(pin);
  if (pin == A7) return board.readButtonChannel();
  board.advanceUs(FakeBoard::ADC_TIME_US);
  return 0;
}
inline void tone(uint8_t, unsigned int freq) {
  FakeBoard::ToneEvent e = { (int) freq, board.ms() };
  board.tones.push_back(e);
}
inline void noTone(uint8_t) {}

// ── Serial ──────────────────────────────────────────────────────────────────
struct FakeSerial {
  void begin(long) {}
  void put(const std::string &s) {
    board.serial += s;
    if (board.traceSerial) fputs(s.c_str(), stdout);
  }
  void print(const char *s) { put(s); }
  void print(const __FlashStringHelper *s) { put((const char *) s); }
  void print(char c) { put(std::string(1, c)); }
  void print(int v) { put(std::to_string(v)); }
  void print(long v) { put(std::to_string(v)); }
  void print(unsigned v) { put(std::to_string(v)); }
  void print(unsigned long v) { put(std::to_string(v)); }
  void println() { put("\n"); }
  template <typename T> void println(T v) { print(v); put("\n"); }
};
extern FakeSerial Serial;

#endif  // ARDUINO_SHIM_H
